Sillybutts/SLAB/SLAB v4 Release/STLs/Green/TopCover.stl

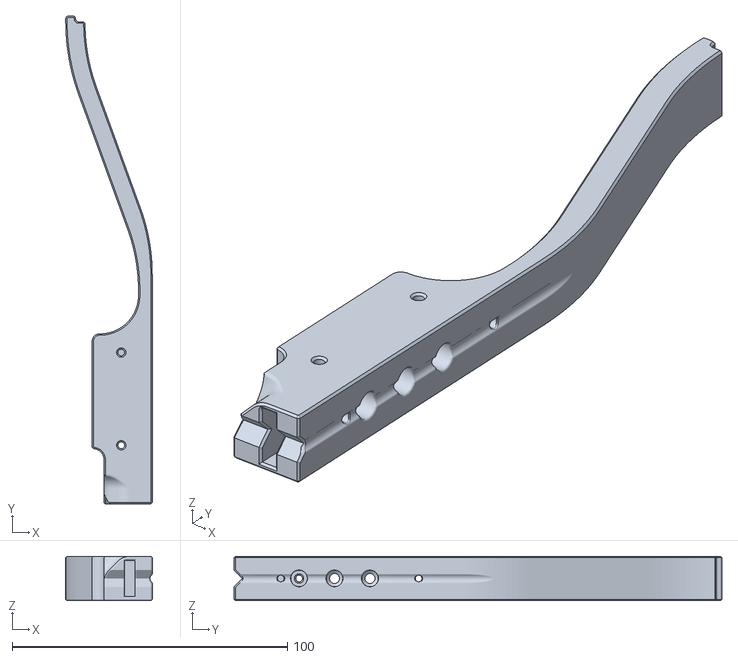
[picture p50: CAD file, 2023-04-10]
SLAB v4 Release/STLs/Green/TopCover.stl
31.4 x 177.2 x 16.1
