Sillybutts/SLAB/SLAB v4 Release/STLs/Orange/Trigger_ExperimentalMoreClearanceWithLever.stl

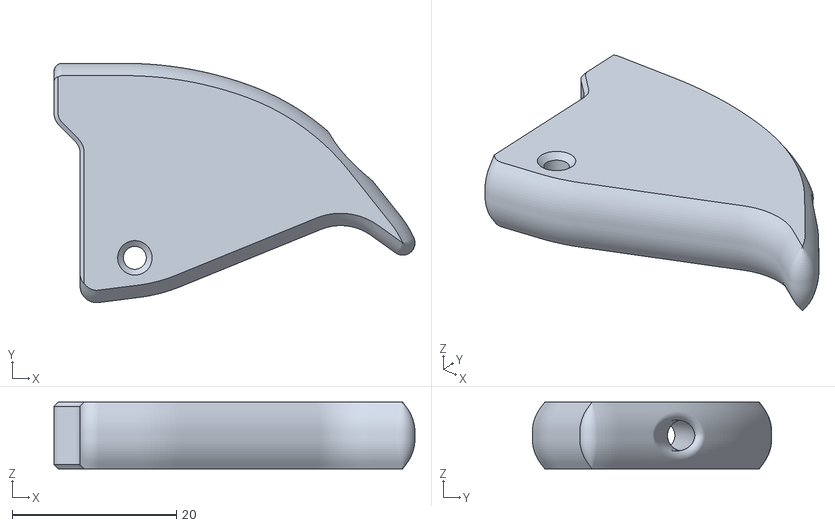
[picture p51: CAD file, 2023-03-18]
SLAB v4 Release/STLs/Orange/Trigger_ExperimentalMoreClearanceWithLever.stl
44.0 x 29.2 x 8.12
