Sillybutts/SLAB/SLAB v4 Release/STLs/White/RailSpacer.stl

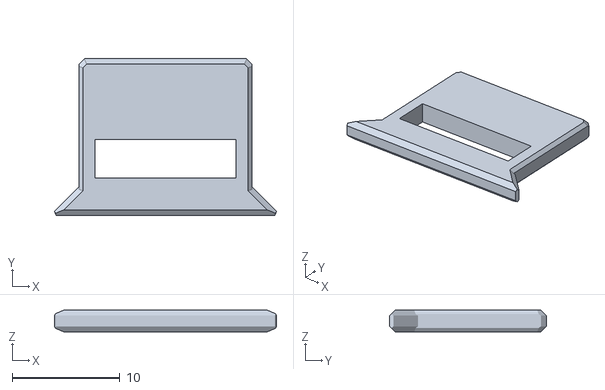
[picture p52: CAD file, 2023-03-18]
SLAB v4 Release/STLs/White/RailSpacer.stl
20.6 x 14.5 x 2.00
