Sillybutts/SLAB/v3 BAR BETA VERSION/v3 BAR BETA VERSION STLs/Black/StockButt.stl

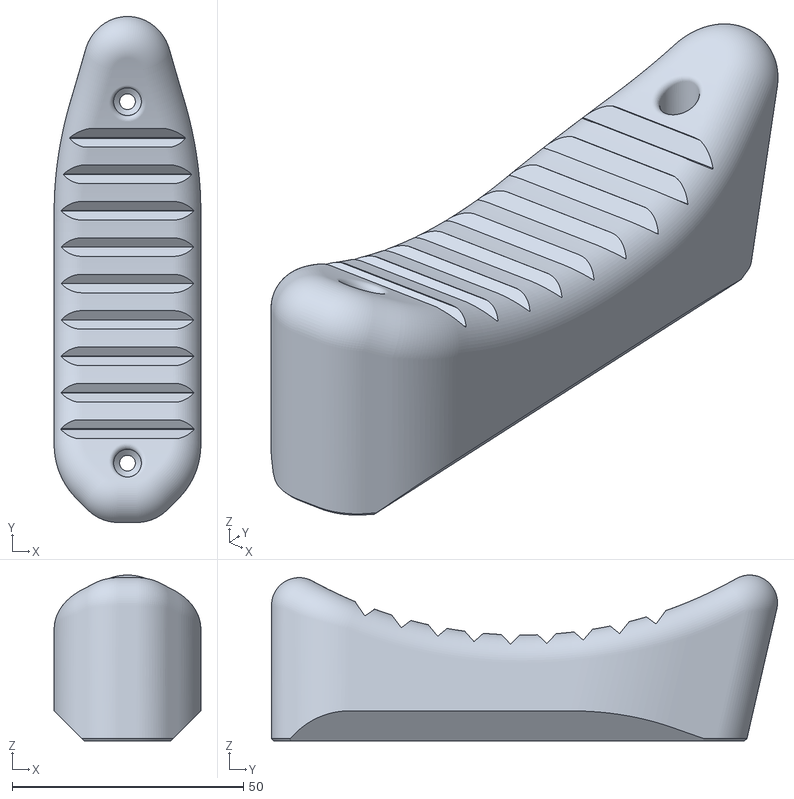
[picture p53: CAD file, 2022-07-23]
v3 BAR BETA VERSION/v3 BAR BETA VERSION STLs/Black/StockButt.stl
31.8 x 109.5 x 35.9
