Sillybutts/SLAB/v3 BAR BETA VERSION/v3 BAR BETA VERSION STLs/Green/New Backstrap.stl

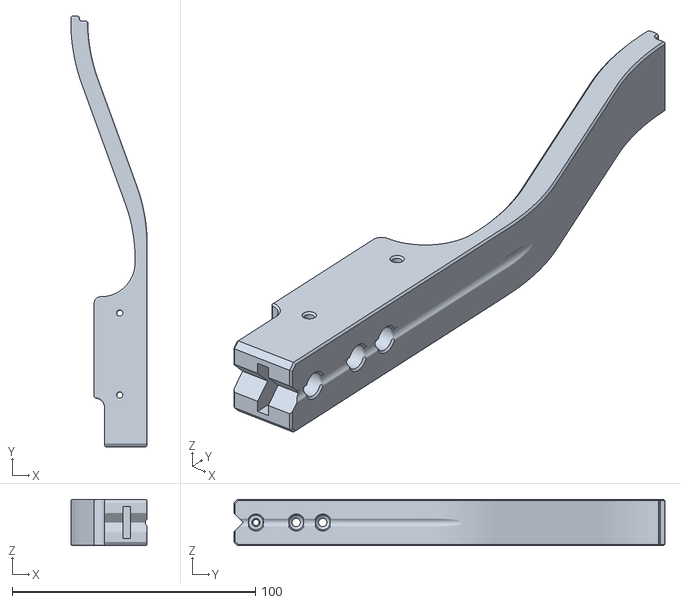
[picture p54: CAD file, 2022-08-06]
v3 BAR BETA VERSION/v3 BAR BETA VERSION STLs/Green/New Backstrap.stl
31.4 x 177.2 x 19.1
