Sillybutts/SLAB/v3 BAR BETA VERSION/v3 BAR BETA VERSION STLs/Orange/Bottlenose wRail.stl

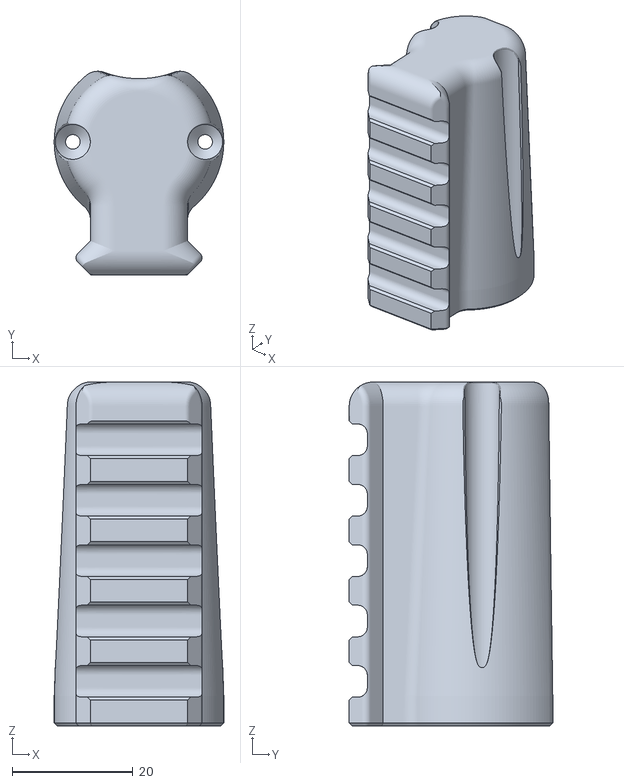
[picture p55: CAD file, 2022-08-02]
v3 BAR BETA VERSION/v3 BAR BETA VERSION STLs/Orange/Bottlenose wRail.stl
28.1 x 33.7 x 57.0
