Sillybutts/SLAB/v3 BAR BETA VERSION/v3 BAR BETA VERSION STLs/White/New Backrail.stl

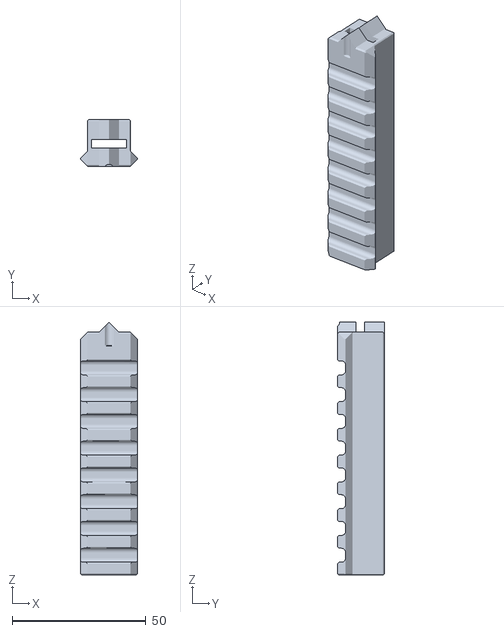
[picture p56: CAD file, 2022-08-06]
v3 BAR BETA VERSION/v3 BAR BETA VERSION STLs/White/New Backrail.stl
21.2 x 17.5 x 94.6
