Sillybutts/SLAB/SLAB Metric prints for the V4 3-10-2023/STLs/METRIC_Ram 7mmID o-ring.stl

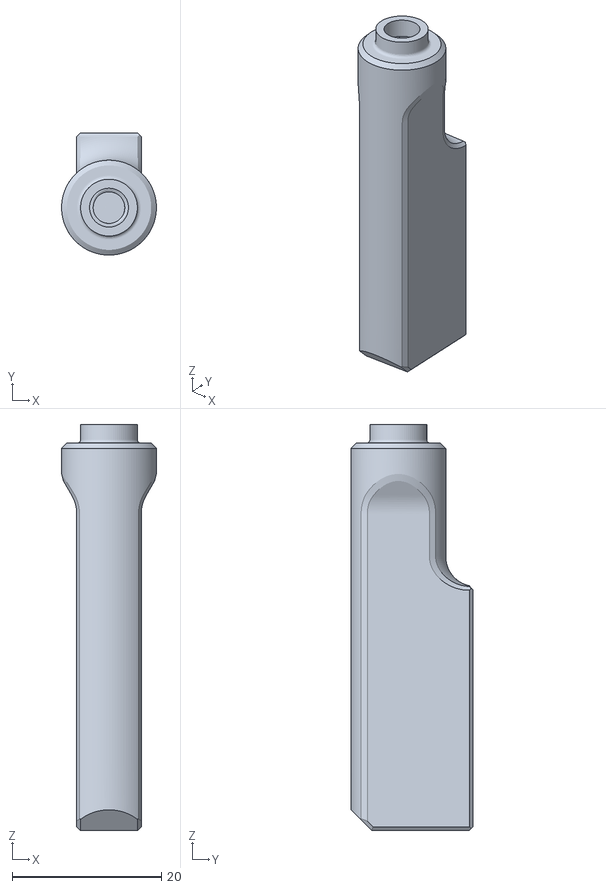
[picture p57: CAD file, 2023-03-10]
SLAB Metric prints for the V4 3-10-2023/STLs/METRIC_Ram 7mmID o-ring.stl
12.7 x 16.4 x 54.3
