Sillybutts/SLAB/SLAB v4 Release/STLs/Black/GripPanel_L.stl

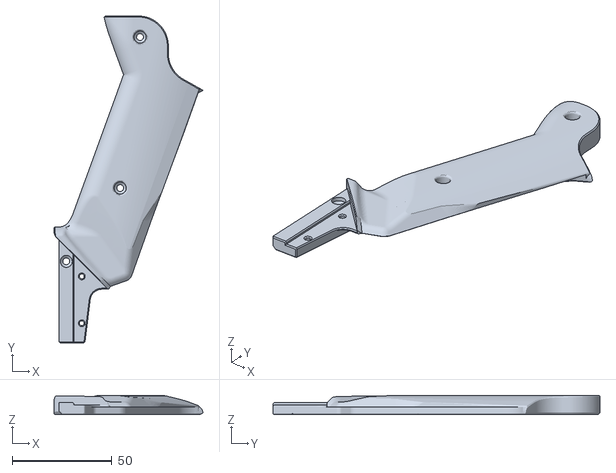
[picture p58: CAD file, 2023-03-18]
SLAB v4 Release/STLs/Black/GripPanel_L.stl
74.7 x 163.8 x 9.53
