Sillybutts/SLAB/SLAB v4 Release/STLs/EXPERIMENTAL AND OPTIONAL/Alternate logos/SideCover_L OLDLOGO.stl

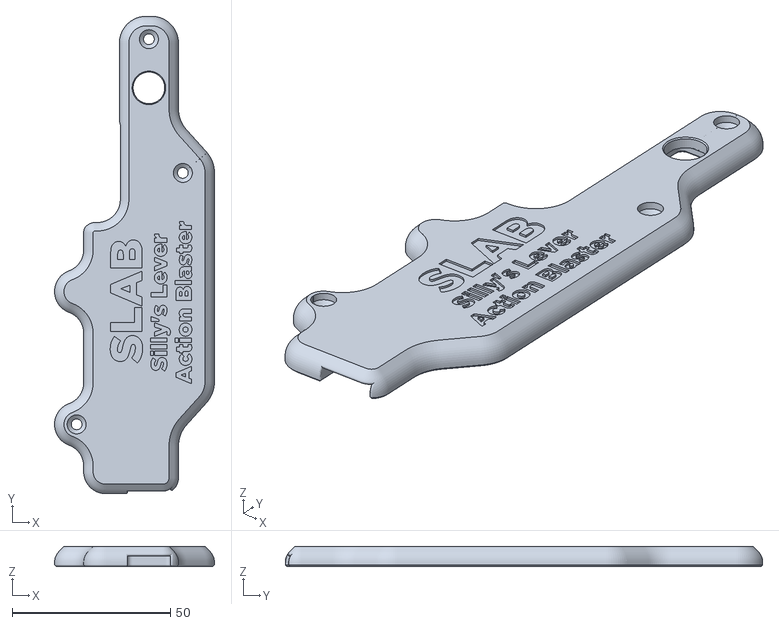
[picture p59: CAD file, 2023-03-18]
SLAB v4 Release/STLs/EXPERIMENTAL AND OPTIONAL/Alternate logos/SideCover_L OLDLOGO.stl
50.6 x 151.0 x 6.36
