Sillybutts/SLAB/SLAB v4 Release/STLs/EXPERIMENTAL AND OPTIONAL/Angled Talon magwell/Angled Magwell.stl

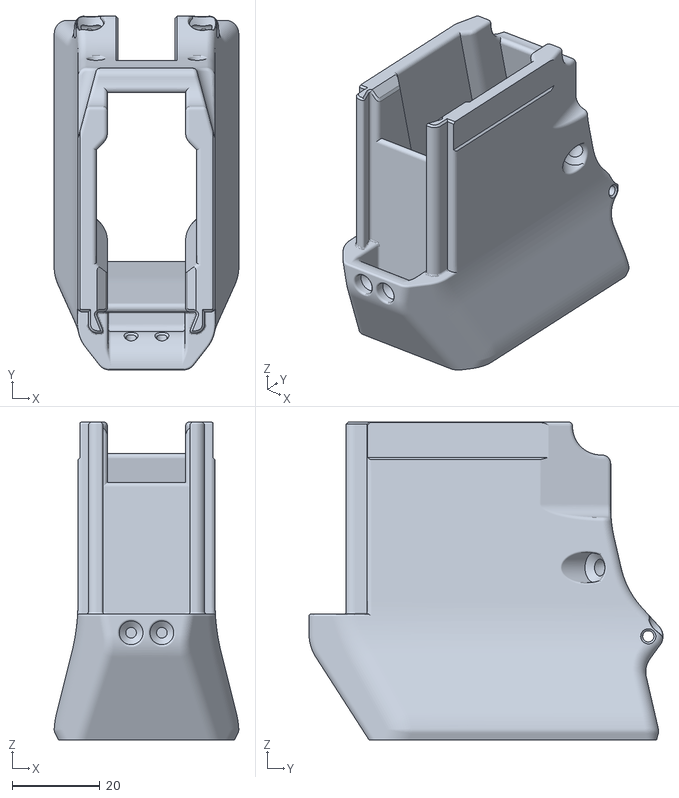
[picture p60: CAD file, 2023-03-18]
SLAB v4 Release/STLs/EXPERIMENTAL AND OPTIONAL/Angled Talon magwell/Angled Magwell.stl
42.0 x 80.6 x 72.4
