Sillybutts/SLAB/SLAB v4 Release/STLs/EXPERIMENTAL AND OPTIONAL/Long plunger rods that stick out the front/Muzzle_BottlenoseRail.stl

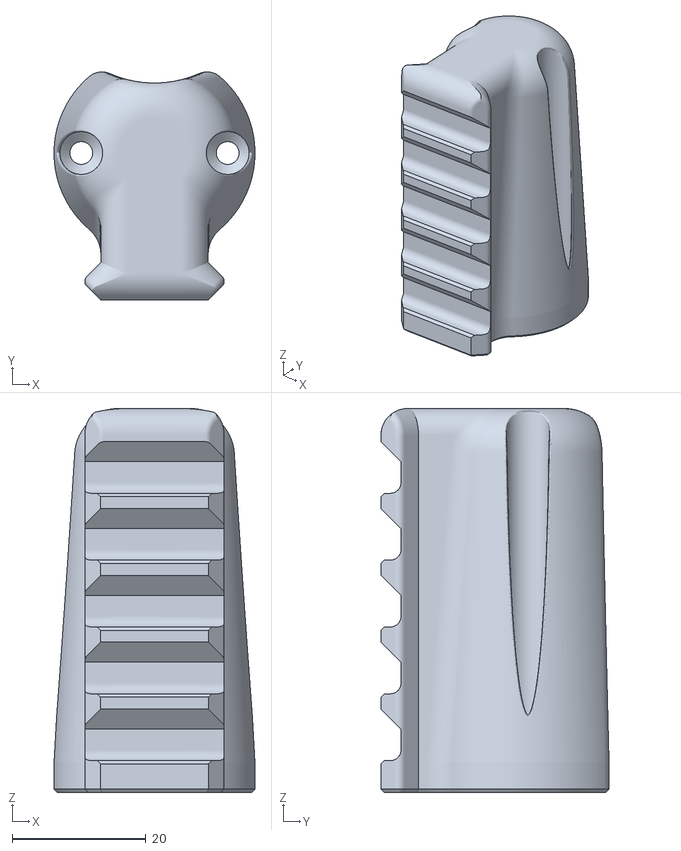
[picture p61: CAD file, 2023-03-18]
SLAB v4 Release/STLs/EXPERIMENTAL AND OPTIONAL/Long plunger rods that stick out the front/Muzzle_BottlenoseRail.stl
30.1 x 34.2 x 57.5
