Sillybutts/SLAB/SLAB v4 Release/STLs/EXPERIMENTAL AND OPTIONAL/Split lever for 150x150mm printers/Split_Lever_Standard.stl

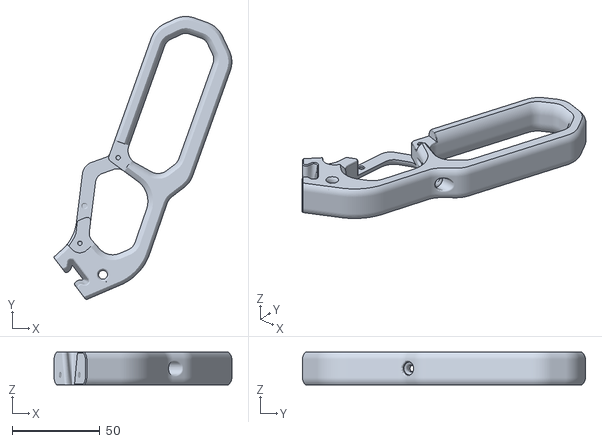
[picture p62: CAD file, 2023-03-18]
SLAB v4 Release/STLs/EXPERIMENTAL AND OPTIONAL/Split lever for 150x150mm printers/Split_Lever_Standard.stl
101.3 x 161.3 x 18.5
