Sillybutts/SLAB/SLAB v4 Release/STLs/Green/Handguard wShortPicatinny.stl

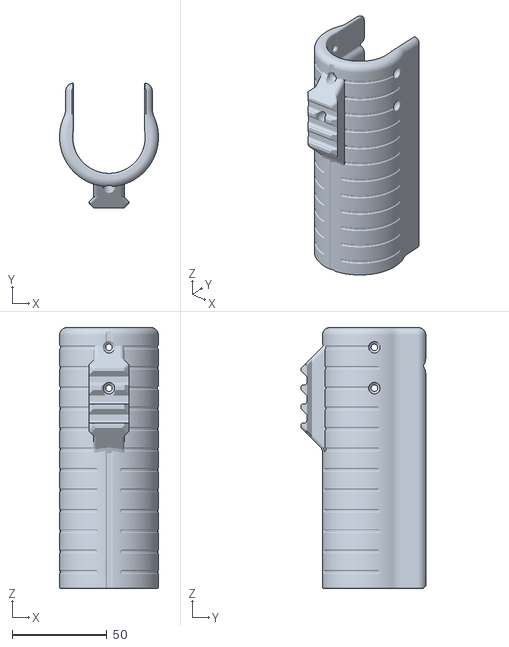
[picture p63: CAD file, 2023-04-10]
SLAB v4 Release/STLs/Green/Handguard wShortPicatinny.stl
52.1 x 65.6 x 137.4
