Sillybutts/SLAB/SLAB v4 Release/STLs/Orange/RodCapKeeper.stl

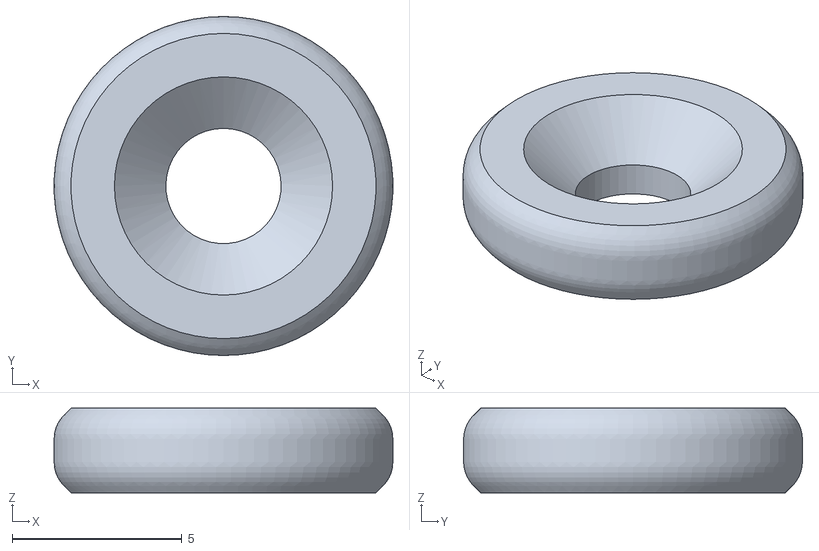
[picture p64: CAD file, 2023-03-18]
SLAB v4 Release/STLs/Orange/RodCapKeeper.stl
9.99 x 10.00 x 2.50
