Sillybutts/SLAB/SLAB v4 Release/STLs/White/RailB.stl

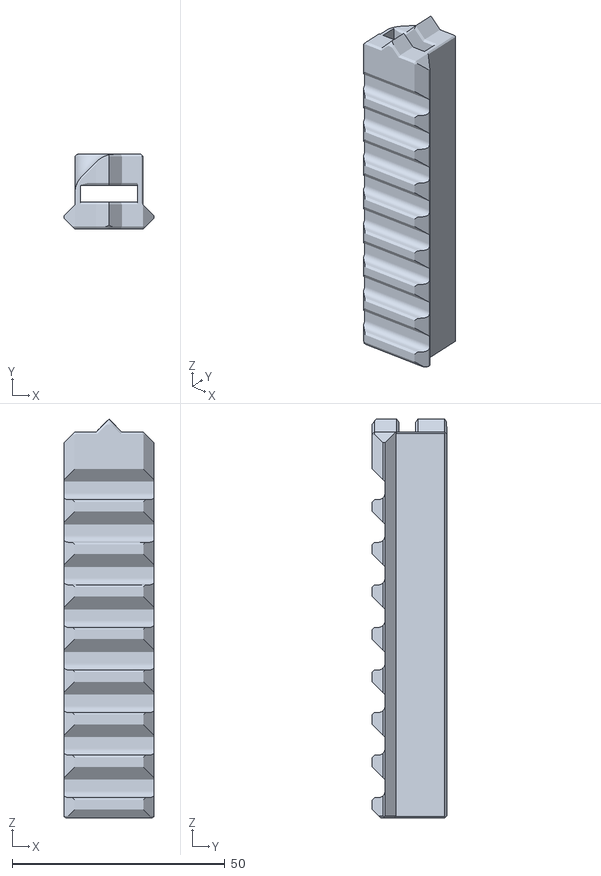
[picture p65: CAD file, 2023-03-18]
SLAB v4 Release/STLs/White/RailB.stl
21.2 x 17.5 x 93.8
