Sillybutts/SLAB/v3 BAR BETA VERSION/v3 BAR BETA VERSION STLs/Green/Handguard wBackstop.stl

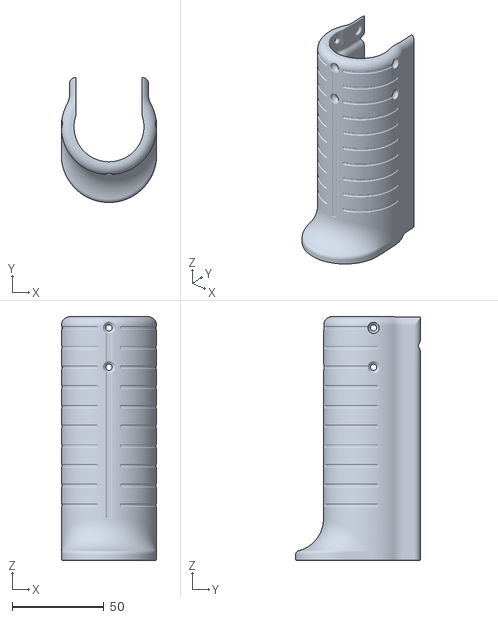
[picture p66: CAD file, 2022-08-06]
v3 BAR BETA VERSION/v3 BAR BETA VERSION STLs/Green/Handguard wBackstop.stl
52.1 x 68.3 x 133.2
