Sillybutts/SLAB/SLAB Metric prints for the V4 3-10-2023/STLs/METRIC_OnePieceTurnaround.stl

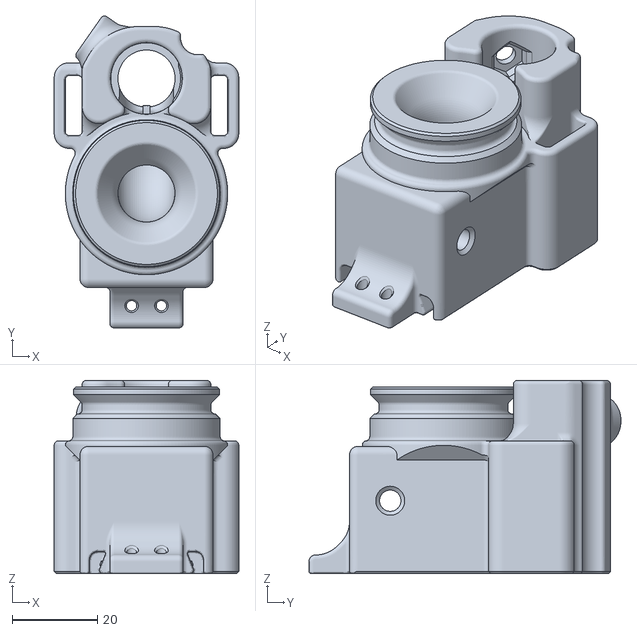
[picture p67: CAD file, 2023-03-10]
SLAB Metric prints for the V4 3-10-2023/STLs/METRIC_OnePieceTurnaround.stl
43.3 x 73.2 x 45.4
