Sillybutts/SLAB/SLAB v4 Release/STLs/EXPERIMENTAL AND OPTIONAL/Alternate logos/Nameplate.stl

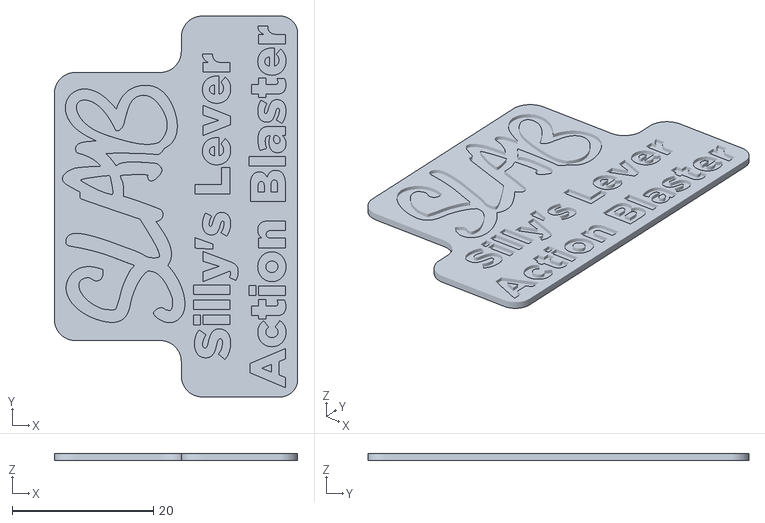
[picture p68: CAD file, 2023-03-18]
SLAB v4 Release/STLs/EXPERIMENTAL AND OPTIONAL/Alternate logos/Nameplate.stl
34.5 x 54.0 x 1.00
