Sillybutts/SLAB/SLAB v4 Release/STLs/EXPERIMENTAL AND OPTIONAL/Long plunger rods that stick out the front/Long PlungerRod ARMED.stl

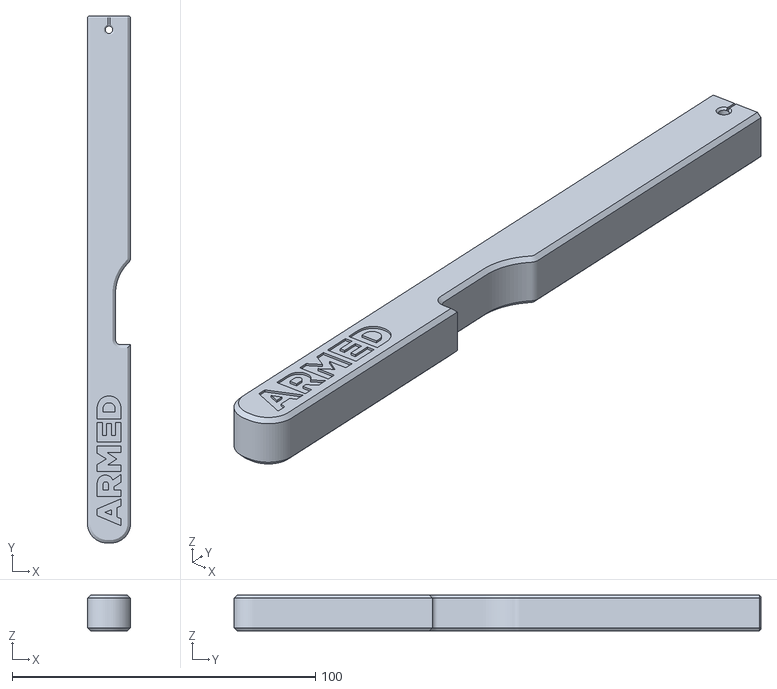
[picture p69: CAD file, 2023-03-18]
SLAB v4 Release/STLs/EXPERIMENTAL AND OPTIONAL/Long plunger rods that stick out the front/Long PlungerRod ARMED.stl
14.3 x 173.8 x 11.8
