Sillybutts/SLAB/SLAB v4 Release/STLs/EXPERIMENTAL AND OPTIONAL/No stock/StockCoreA Stockless.stl

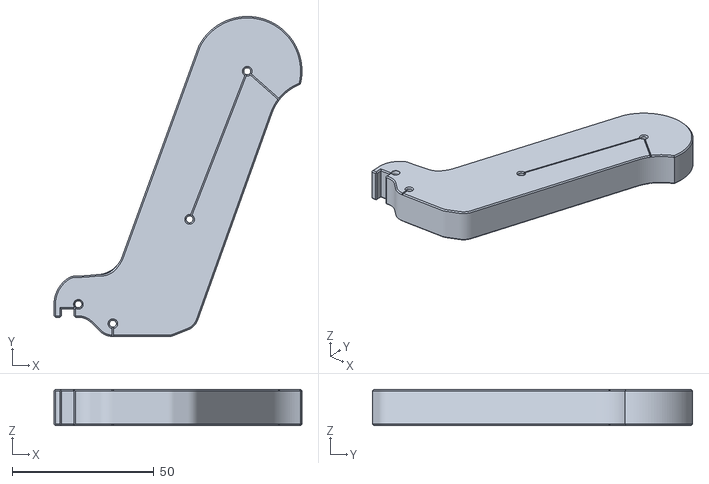
[picture p70: CAD file, 2023-03-18]
SLAB v4 Release/STLs/EXPERIMENTAL AND OPTIONAL/No stock/StockCoreA Stockless.stl
87.3 x 112.7 x 12.7
