Sillybutts/SLAB/SLAB v4 Release/STLs/EXPERIMENTAL AND OPTIONAL/Split lever for 150x150mm printers/Split_Lever_LeverTop.stl

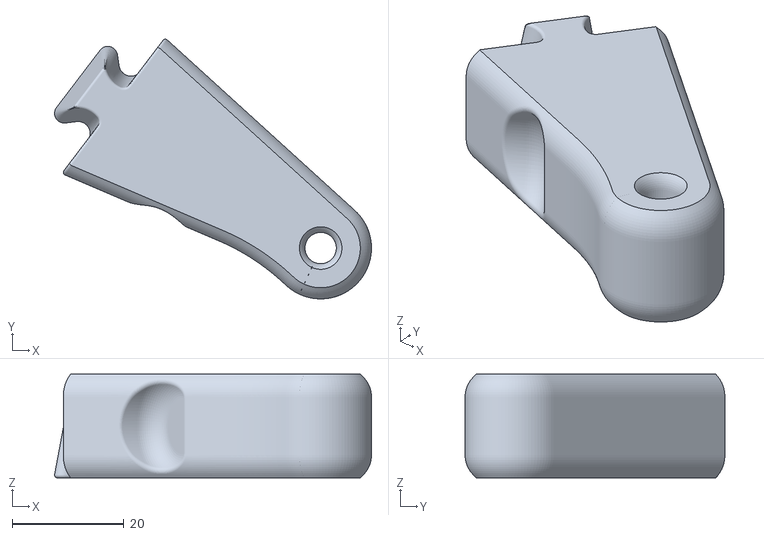
[picture p71: CAD file, 2023-03-18]
SLAB v4 Release/STLs/EXPERIMENTAL AND OPTIONAL/Split lever for 150x150mm printers/Split_Lever_LeverTop.stl
56.6 x 46.4 x 18.5
