Sillybutts/SLAB/SLAB v4 Release/STLs/Green/MuzzleB.stl

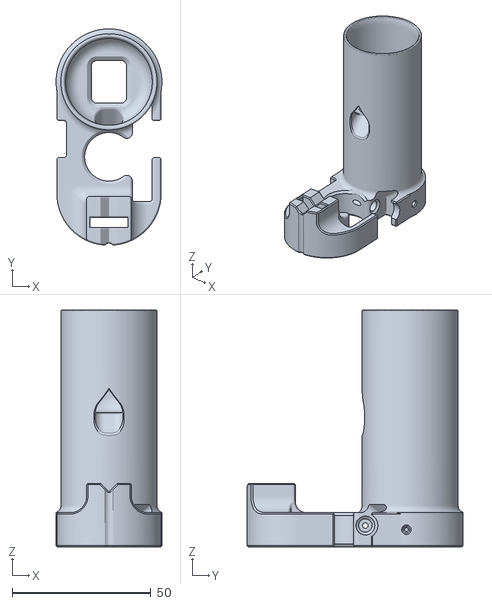
[picture p72: CAD file, 2023-03-18]
SLAB v4 Release/STLs/Green/MuzzleB.stl
38.1 x 77.8 x 85.3
