Sillybutts/SLAB/SLAB v4 Release/STLs/Orange/RodCapPivot.stl

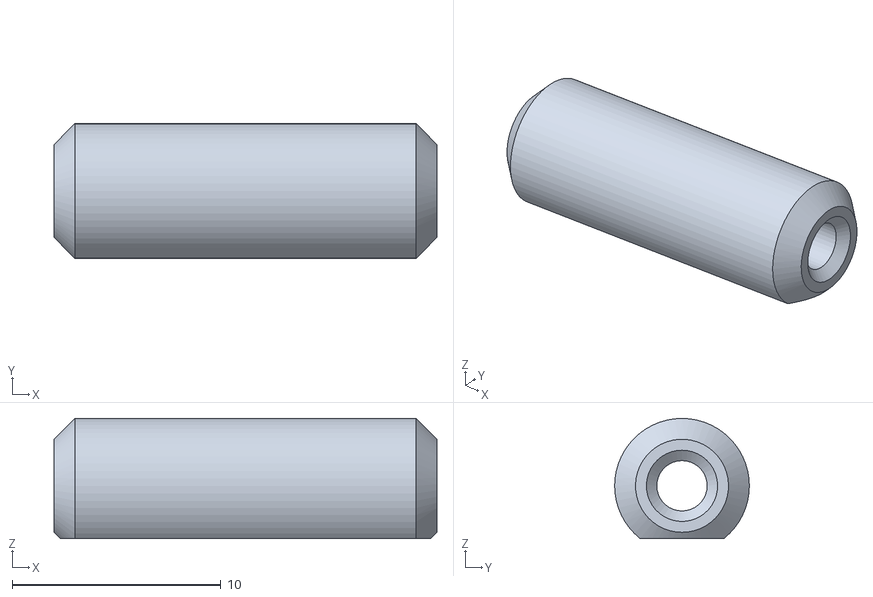
[picture p73: CAD file, 2023-03-18]
SLAB v4 Release/STLs/Orange/RodCapPivot.stl
18.4 x 6.46 x 5.76
