Sillybutts/SLAB/SLAB v4 Release/STLs/White/SightFront.stl

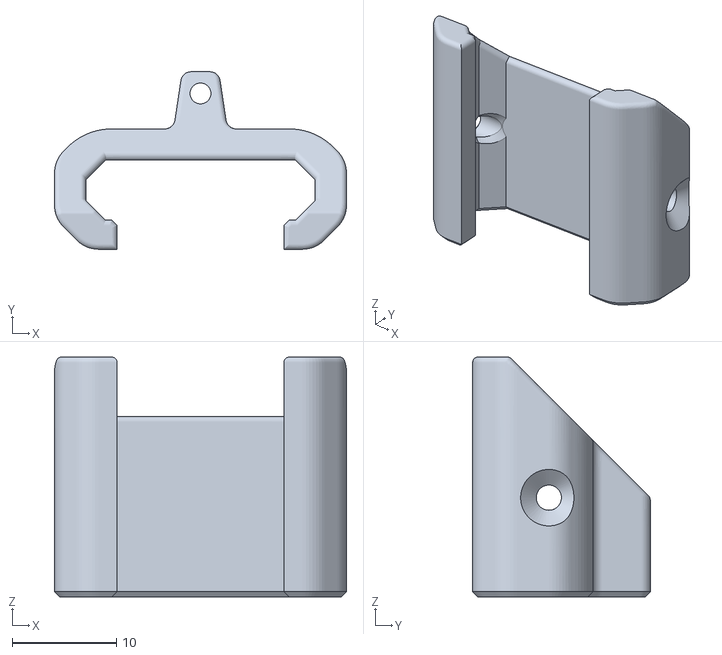
[picture p74: CAD file, 2023-03-18]
SLAB v4 Release/STLs/White/SightFront.stl
28.0 x 17.0 x 23.0
