Sillybutts/SLAB/v3 BAR BETA VERSION/v3 BAR BETA VERSION STLs/Black/Turnaround.stl

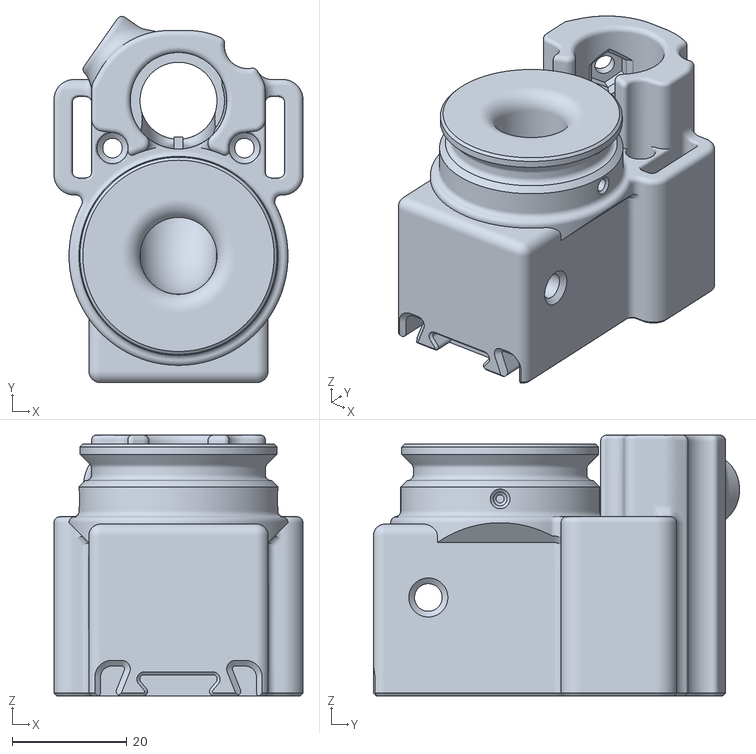
[picture p75: CAD file, 2022-07-20]
v3 BAR BETA VERSION/v3 BAR BETA VERSION STLs/Black/Turnaround.stl
43.3 x 63.7 x 45.4
