Sillybutts/SLAB/v3 BAR BETA VERSION/v3 BAR BETA VERSION STLs/Green/PrintedCotterPin.stl

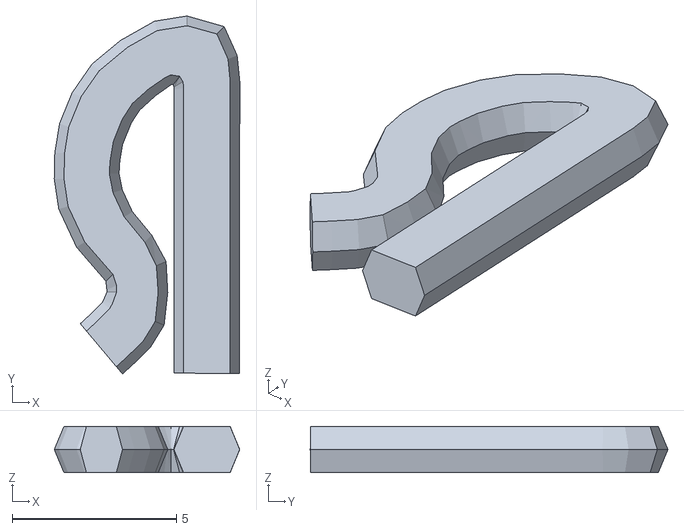
[picture p76: CAD file, 2022-07-25]
v3 BAR BETA VERSION/v3 BAR BETA VERSION STLs/Green/PrintedCotterPin.stl
5.65 x 10.9 x 1.41
