Sillybutts/SLAB/SLAB v4 Release/STLs/Black/PlungerRod.stl

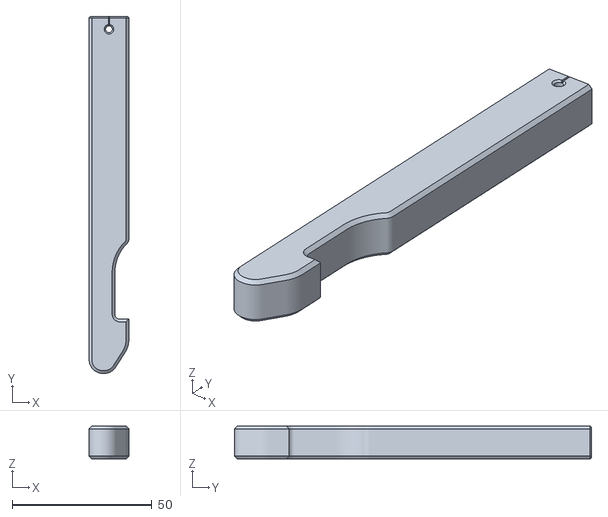
[picture p77: CAD file, 2023-03-18]
SLAB v4 Release/STLs/Black/PlungerRod.stl
14.3 x 127.9 x 11.8
