Sillybutts/SLAB/SLAB v4 Release/STLs/EXPERIMENTAL AND OPTIONAL/MegaXL Spigot SCAR/BarrelCap.stl

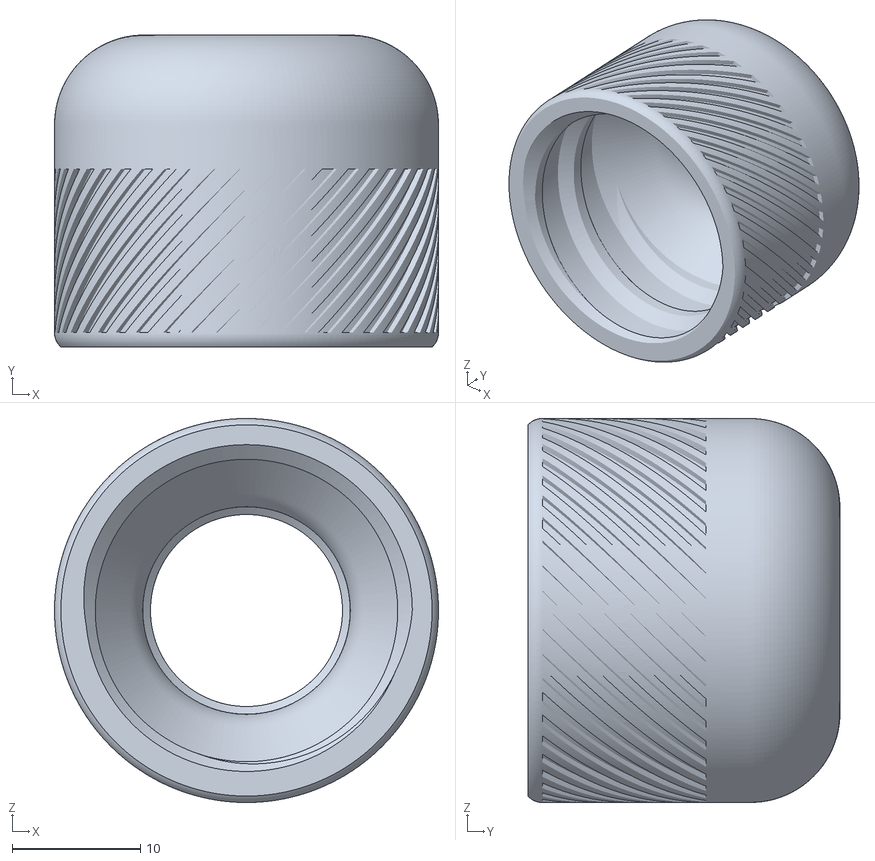
[picture p79: CAD file, 2022-08-25]
SLAB v4 Release/STLs/EXPERIMENTAL AND OPTIONAL/MegaXL Spigot SCAR/BarrelCap.stl
30.0 x 24.4 x 30.0
