Sillybutts/SLAB/SLAB v4 Release/STLs/EXPERIMENTAL AND OPTIONAL/Split lever for 150x150mm printers/Split_Lever_Big.stl

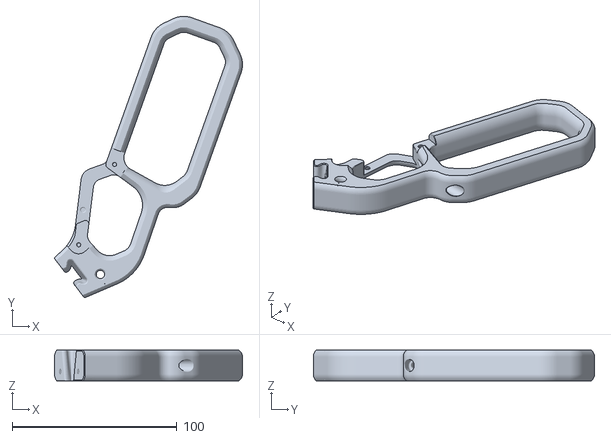
[picture p80: CAD file, 2023-03-18]
SLAB v4 Release/STLs/EXPERIMENTAL AND OPTIONAL/Split lever for 150x150mm printers/Split_Lever_Big.stl
114.1 x 170.8 x 18.5
