Sillybutts/SLAB/SLAB v4 Release/STLs/Green/StockPanelB_R.stl

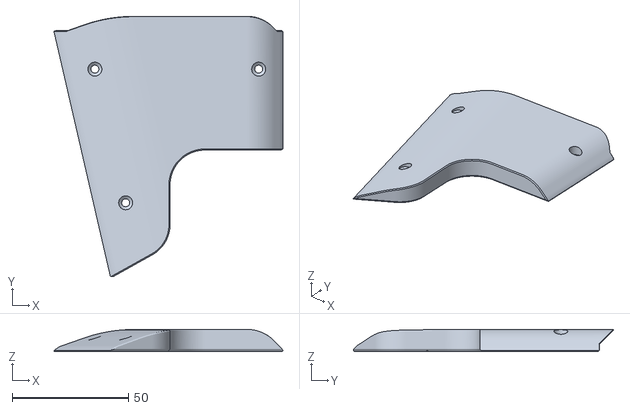
[picture p81: CAD file, 2023-03-18]
SLAB v4 Release/STLs/Green/StockPanelB_R.stl
98.5 x 112.0 x 9.53
