Sillybutts/SLAB/SLAB v4 Release/STLs/White/Railless_RailA.stl

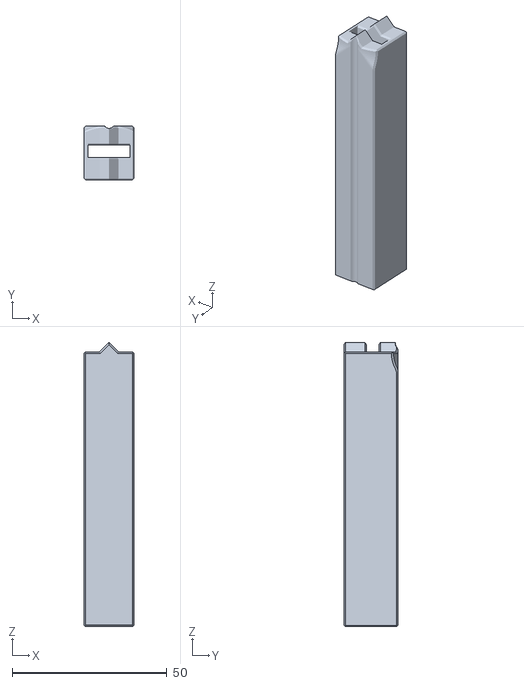
[picture p82: CAD file, 2023-03-18]
SLAB v4 Release/STLs/White/Railless_RailA.stl
16.1 x 17.5 x 91.8
