Sillybutts/SLAB/v3 BAR BETA VERSION/v3 BAR BETA VERSION STLs/Black/PlungerRod ARMED.stl

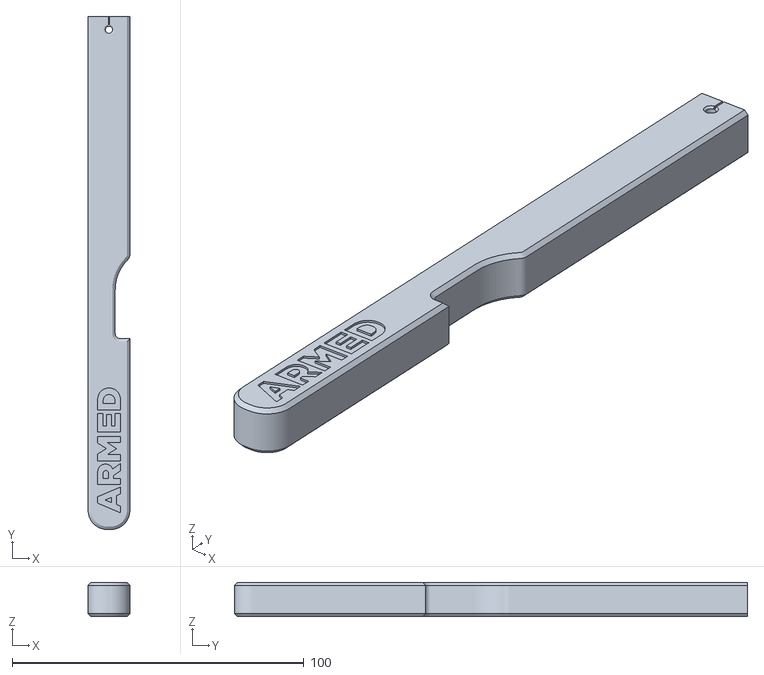
[picture p83: CAD file, 2022-06-17]
v3 BAR BETA VERSION/v3 BAR BETA VERSION STLs/Black/PlungerRod ARMED.stl
14.3 x 175.8 x 11.8
