Sillybutts/SLAB/SLAB Metric prints for the V4 3-10-2023/STLs/SplitTurnaroundCap.stl

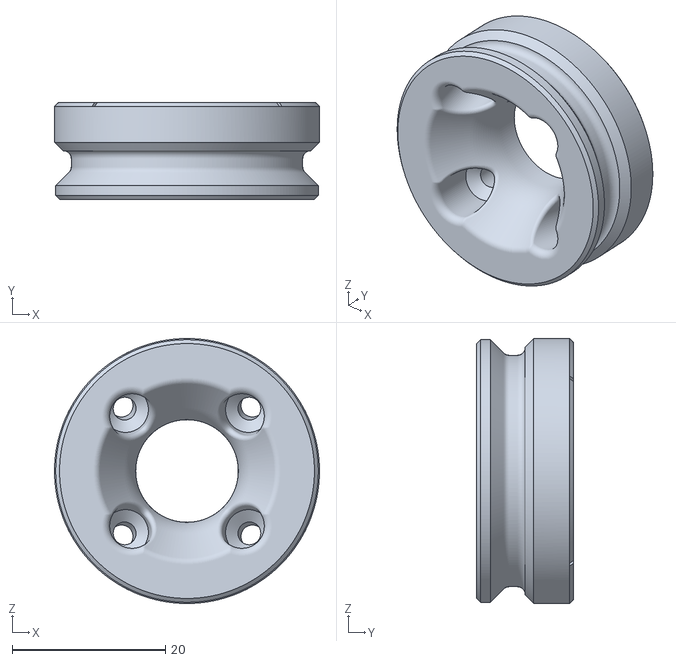
[picture p84: CAD file, 2023-02-27]
SLAB Metric prints for the V4 3-10-2023/STLs/SplitTurnaroundCap.stl
34.6 x 12.7 x 34.6
