Sillybutts/SLAB/SLAB v4 Release/STLs/EXPERIMENTAL AND OPTIONAL/Long plunger rods that stick out the front/Muzzle_Bottlenose.stl

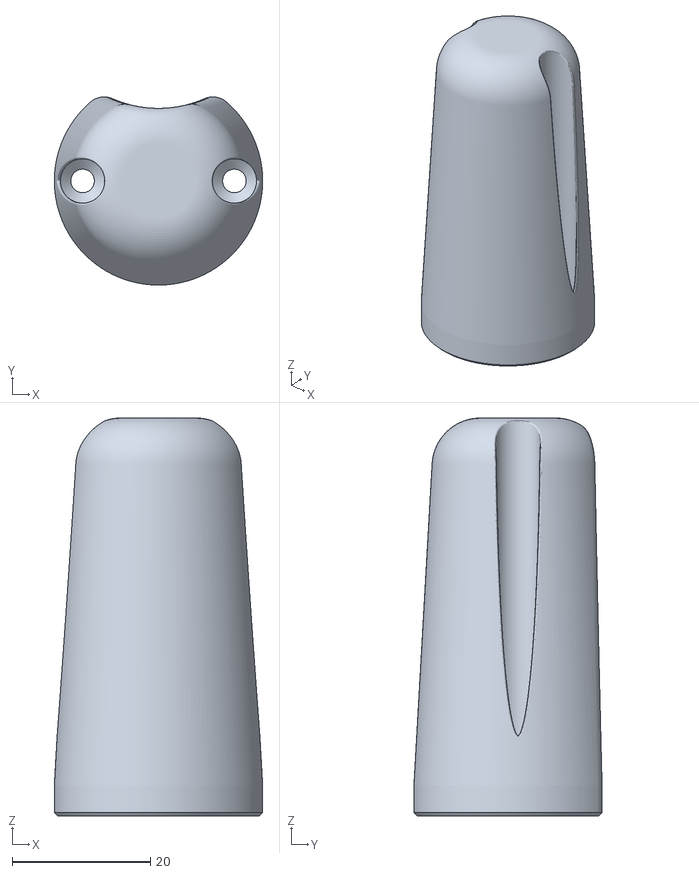
[picture p85: CAD file, 2023-03-18]
SLAB v4 Release/STLs/EXPERIMENTAL AND OPTIONAL/Long plunger rods that stick out the front/Muzzle_Bottlenose.stl
30.1 x 27.2 x 57.5
