Sillybutts/SLAB/SLAB v4 Release/STLs/Green/StockPanelA_R.stl

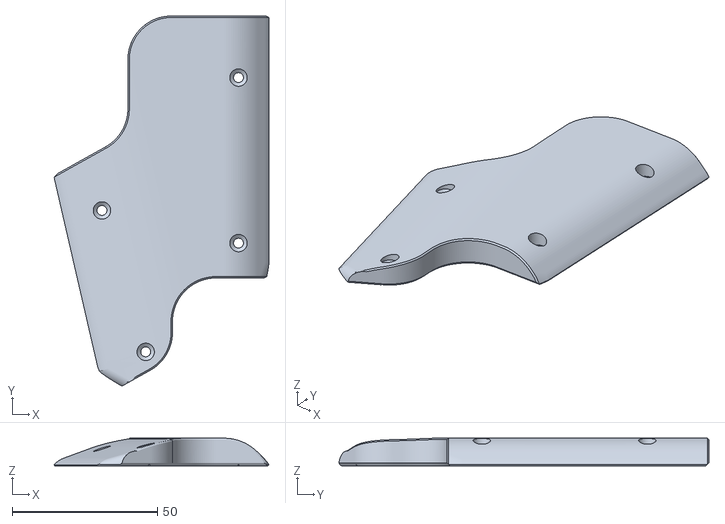
[picture p86: CAD file, 2023-03-18]
SLAB v4 Release/STLs/Green/StockPanelA_R.stl
74.0 x 127.4 x 9.53
