Sillybutts/SLAB/SLAB v4 Release/STLs/Orange/Ram_FlatFace_Tighter.stl

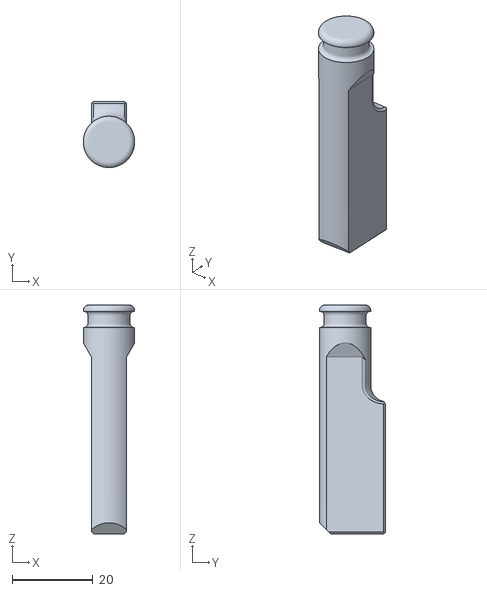
[picture p87: CAD file, 2023-03-18]
SLAB v4 Release/STLs/Orange/Ram_FlatFace_Tighter.stl
12.7 x 16.4 x 56.6
