Sillybutts/SLAB/SLAB v4 Release/STLs/White/Railless_RailB.stl

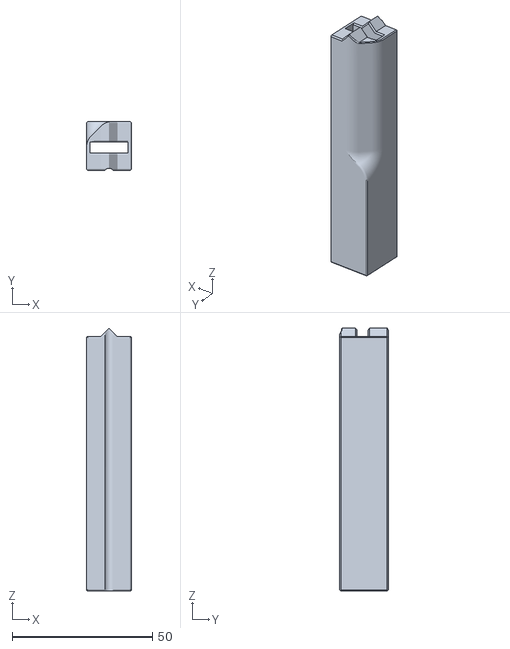
[picture p88: CAD file, 2023-03-18]
SLAB v4 Release/STLs/White/Railless_RailB.stl
16.1 x 17.5 x 93.8
