Sillybutts/SLAB/v3 BAR BETA VERSION/v3 BAR BETA VERSION STLs/Black/PlungerRod BLANK.stl

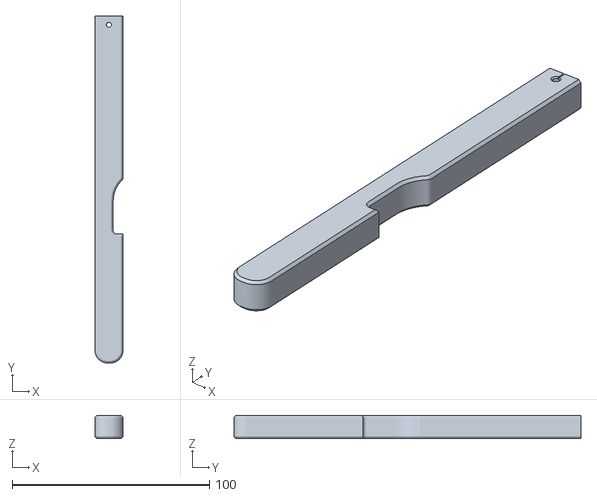
[picture p89: CAD file, 2022-06-17]
v3 BAR BETA VERSION/v3 BAR BETA VERSION STLs/Black/PlungerRod BLANK.stl
14.3 x 175.8 x 11.8
