Sillybutts/SLAB/SLAB v4 Release/STLs/Black/OptionalTopCoverTopRail.stl

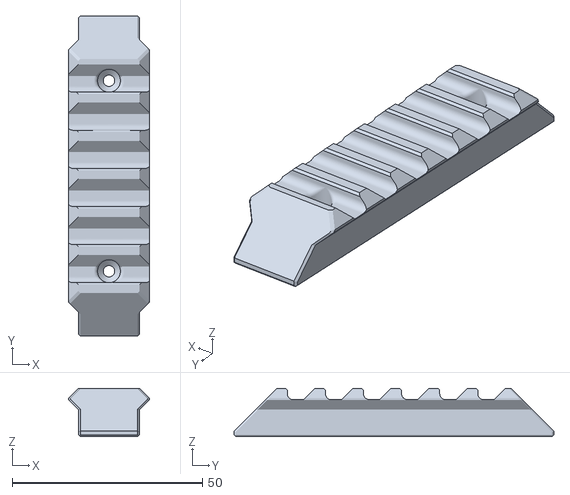
[picture p90: CAD file, 2023-03-18]
SLAB v4 Release/STLs/Black/OptionalTopCoverTopRail.stl
21.2 x 84.1 x 12.7
