Sillybutts/SLAB/SLAB v4 Release/STLs/EXPERIMENTAL AND OPTIONAL/Long plunger rods that stick out the front/Muzzle_FrontSlingOpen.stl

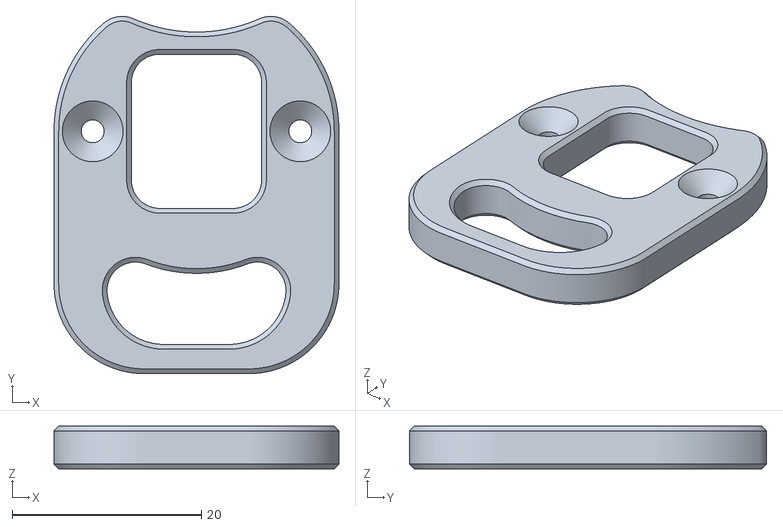
[picture p91: CAD file, 2023-03-18]
SLAB v4 Release/STLs/EXPERIMENTAL AND OPTIONAL/Long plunger rods that stick out the front/Muzzle_FrontSlingOpen.stl
30.1 x 37.7 x 4.50
