Sillybutts/SLAB/SLAB v4 Release/STLs/Green/SideCover_R wLogo.stl

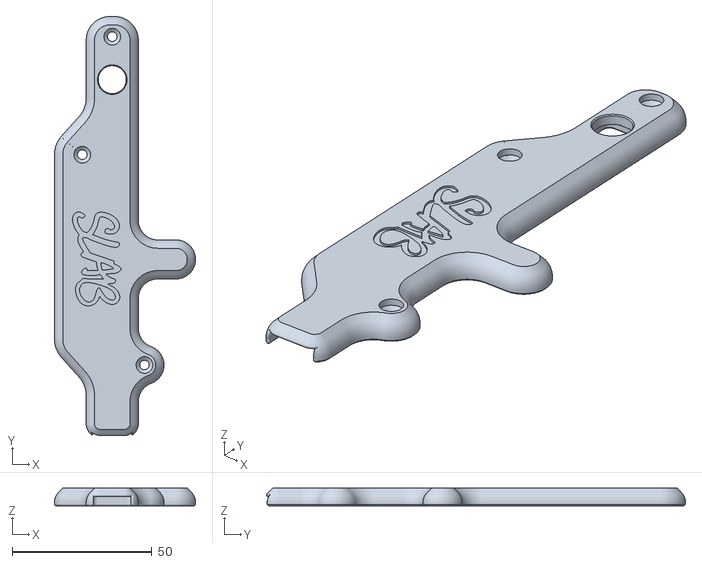
[picture p92: CAD file, 2023-03-18]
SLAB v4 Release/STLs/Green/SideCover_R wLogo.stl
50.6 x 150.2 x 6.36
