Sillybutts/SLAB/SLAB v4 Release/STLs/Orange/Catch.stl

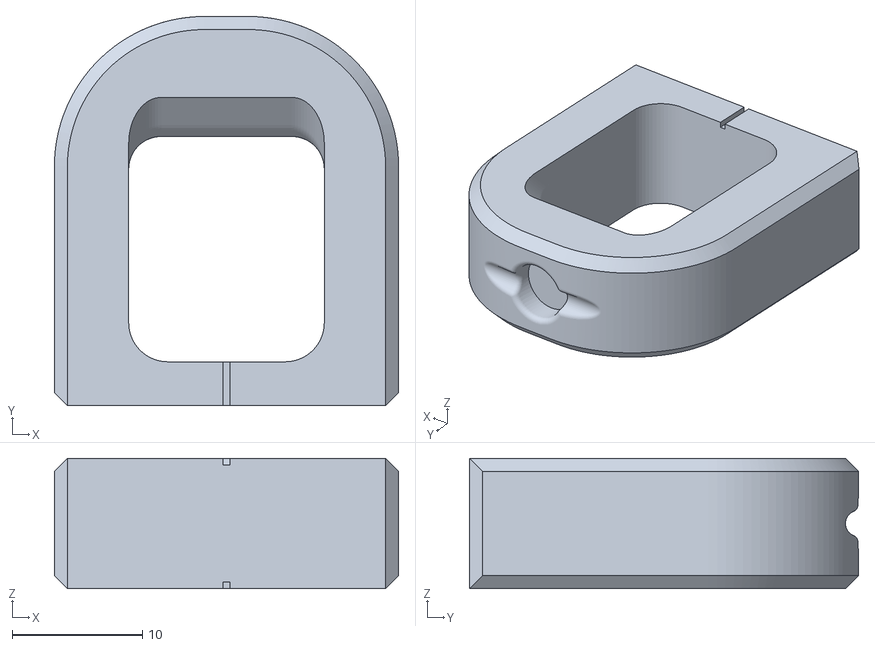
[picture p93: CAD file, 2023-03-18]
SLAB v4 Release/STLs/Orange/Catch.stl
26.4 x 29.8 x 10.0
