Sillybutts/SLAB/SLAB v4 Release/STLs/White/RailA.stl

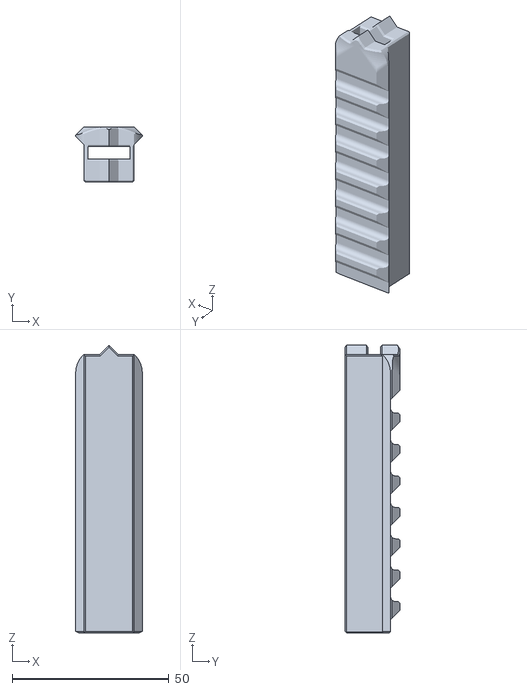
[picture p94: CAD file, 2023-03-18]
SLAB v4 Release/STLs/White/RailA.stl
21.2 x 17.5 x 91.8
