Sillybutts/SLAB/v3 BAR BETA VERSION/v3 BAR BETA VERSION STLs/Green/SideCover_R.stl

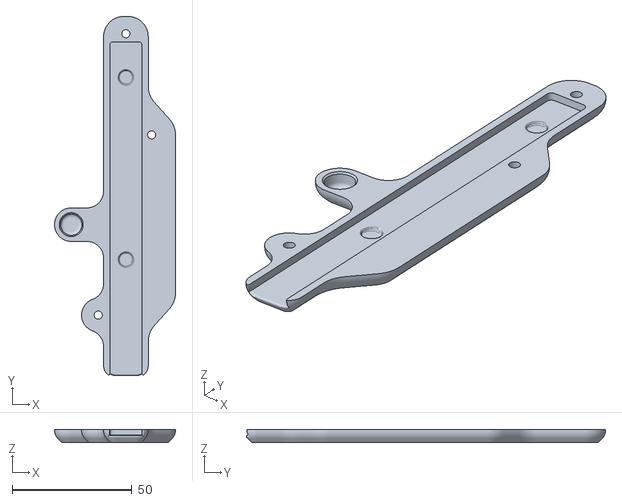
[picture p95: CAD file, 2022-07-03]
v3 BAR BETA VERSION/v3 BAR BETA VERSION STLs/Green/SideCover_R.stl
50.6 x 150.2 x 5.36
