Sillybutts/SLAB/SLAB v4 Release/STLs/Orange/PrimingBarSpacer (PRINT 2).stl

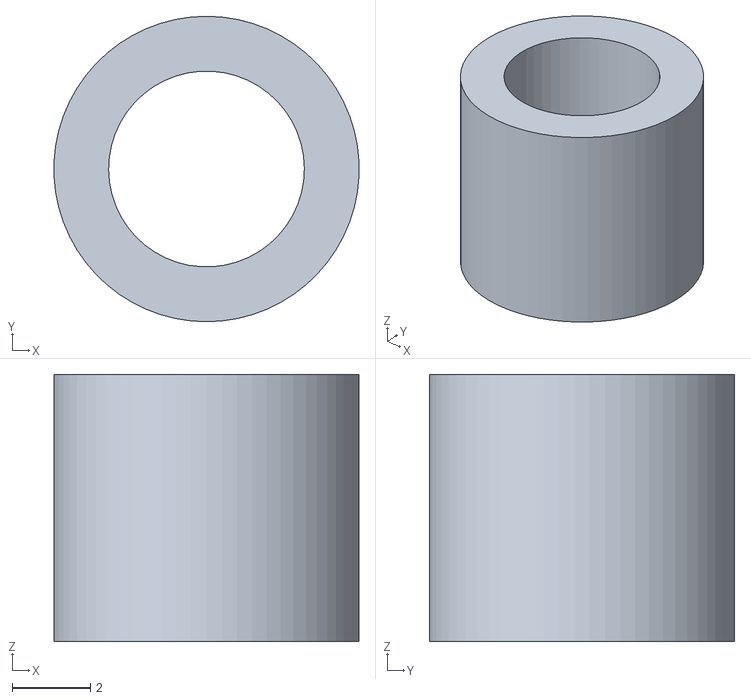
[picture p96: CAD file, 2023-03-18]
SLAB v4 Release/STLs/Orange/PrimingBarSpacer (PRINT 2).stl
7.79 x 7.80 x 6.83
