Sillybutts/SLAB/SLAB v4 Release/STLs/White/Magwell.stl

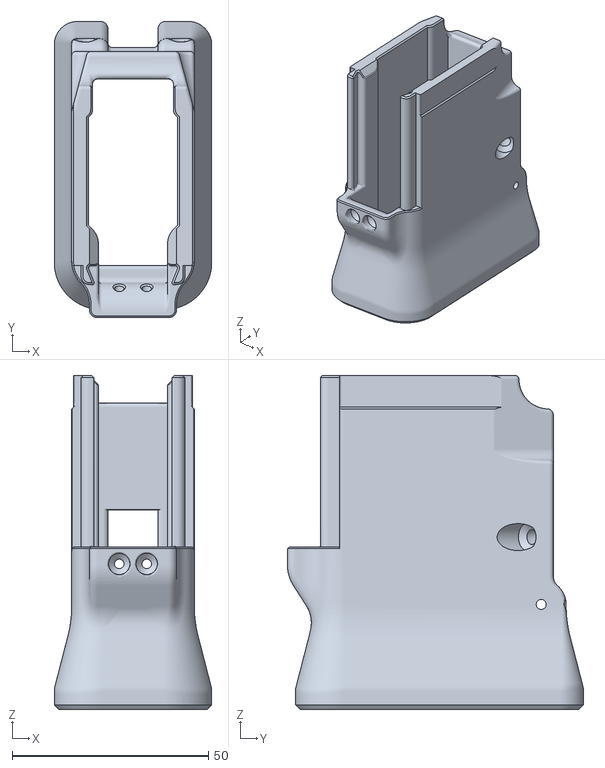
[picture p97: CAD file, 2023-03-18]
SLAB v4 Release/STLs/White/Magwell.stl
40.1 x 75.4 x 85.0
