Sillybutts/SLAB/v3 BAR BETA VERSION/v3 BAR BETA VERSION STLs/Green/SideCover_L.stl

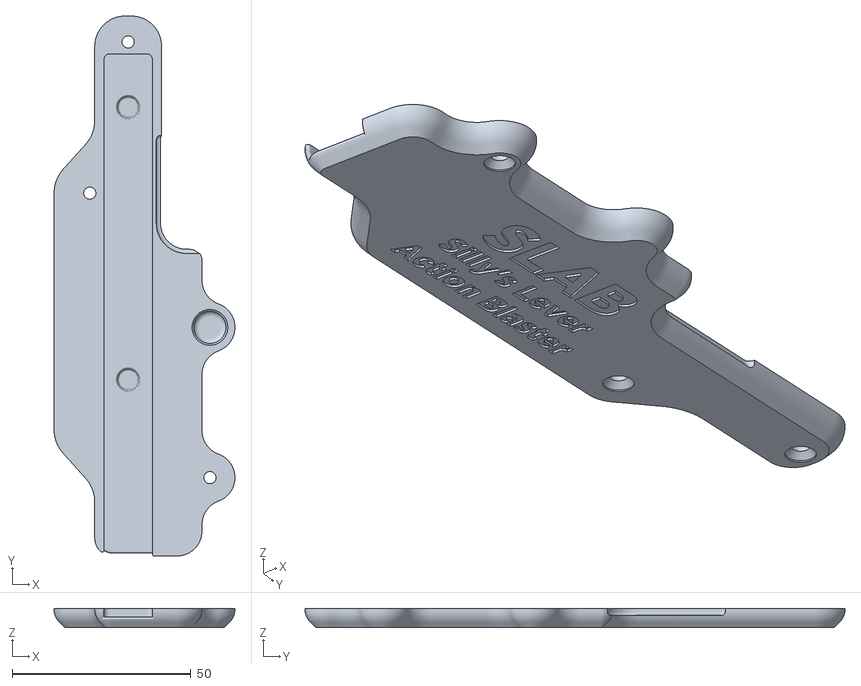
[picture p98: CAD file, 2022-07-03]
v3 BAR BETA VERSION/v3 BAR BETA VERSION STLs/Green/SideCover_L.stl
50.6 x 151.0 x 5.36
