Sillybutts/SLAB/v3 BAR BETA VERSION/v3 BAR BETA VERSION STLs/Orange/Ram.stl

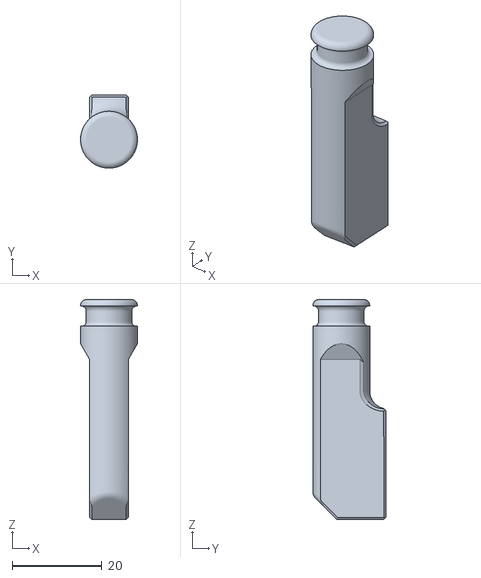
[picture p99: CAD file, 2022-07-20]
v3 BAR BETA VERSION/v3 BAR BETA VERSION STLs/Orange/Ram.stl
12.7 x 16.3 x 49.1
