Sillybutts/SLAB/SLAB v4 Release/STLs/Green/PrimeTransferBar.stl

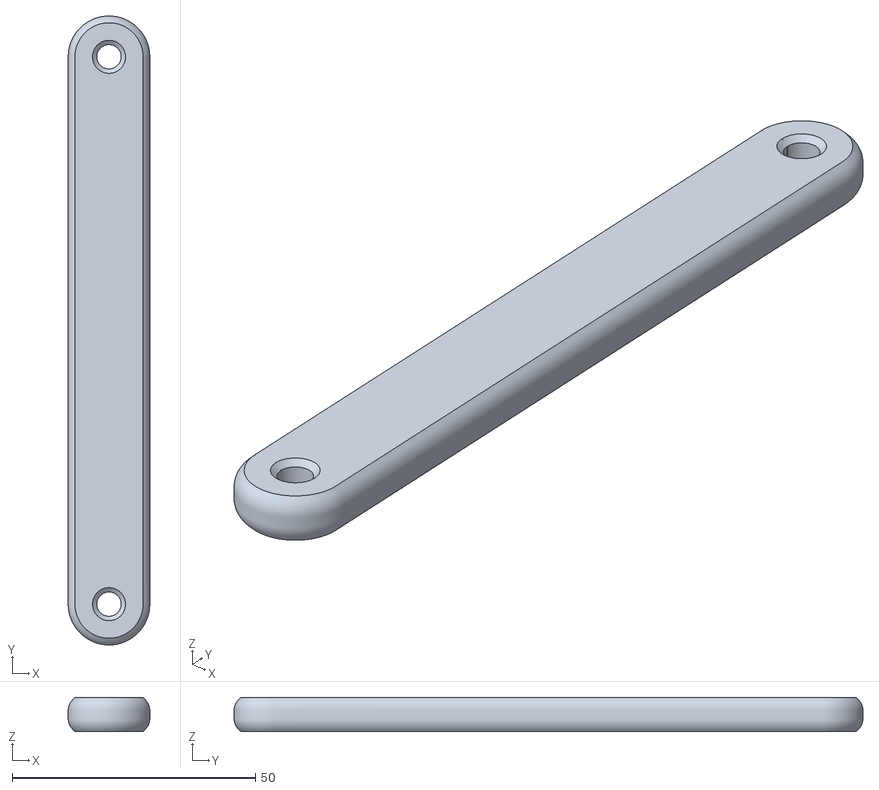
[picture p101: CAD file, 2023-03-18]
SLAB v4 Release/STLs/Green/PrimeTransferBar.stl
16.8 x 129.4 x 7.00
