Sillybutts/SLAB/SLAB v4 Release/STLs/Orange/TriggerBlock.stl

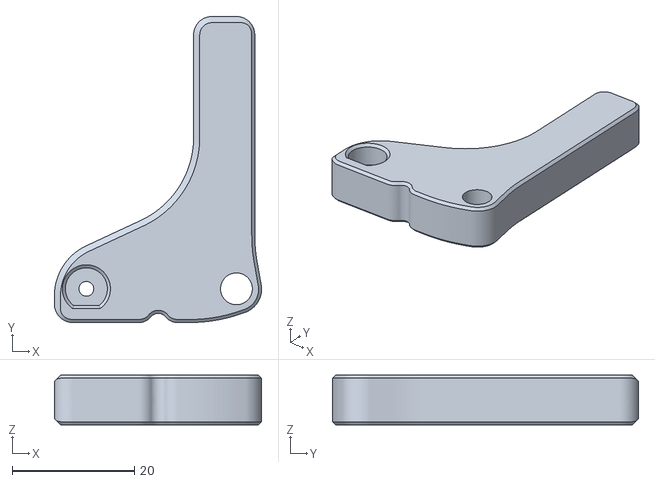
[picture p102: CAD file, 2023-03-18]
SLAB v4 Release/STLs/Orange/TriggerBlock.stl
33.9 x 50.0 x 8.12
