Sillybutts/SLAB/SLAB v4 Release/STLs/White/SightBack.stl

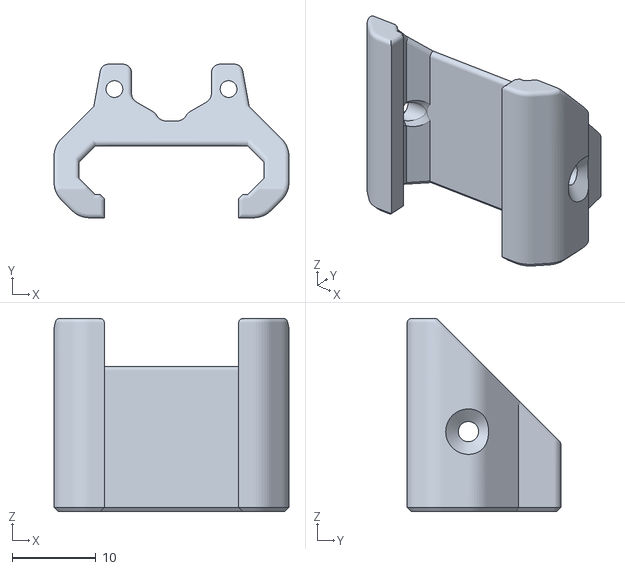
[picture p103: CAD file, 2023-03-18]
SLAB v4 Release/STLs/White/SightBack.stl
28.0 x 18.3 x 23.0
