Sillybutts/SLAB/SLAB v4 Release/STLs/Orange/Muzzle_EndCap.stl

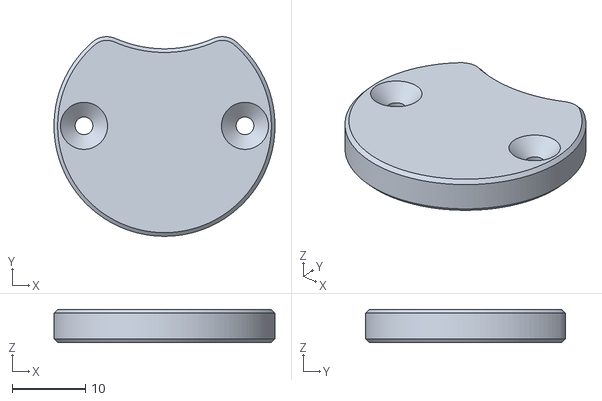
[picture p104: CAD file, 2023-03-18]
SLAB v4 Release/STLs/Orange/Muzzle_EndCap.stl
30.1 x 27.2 x 4.50
