Sillybutts/SLAB/SLAB v4 Release/STLs/White/FeedGuide.stl

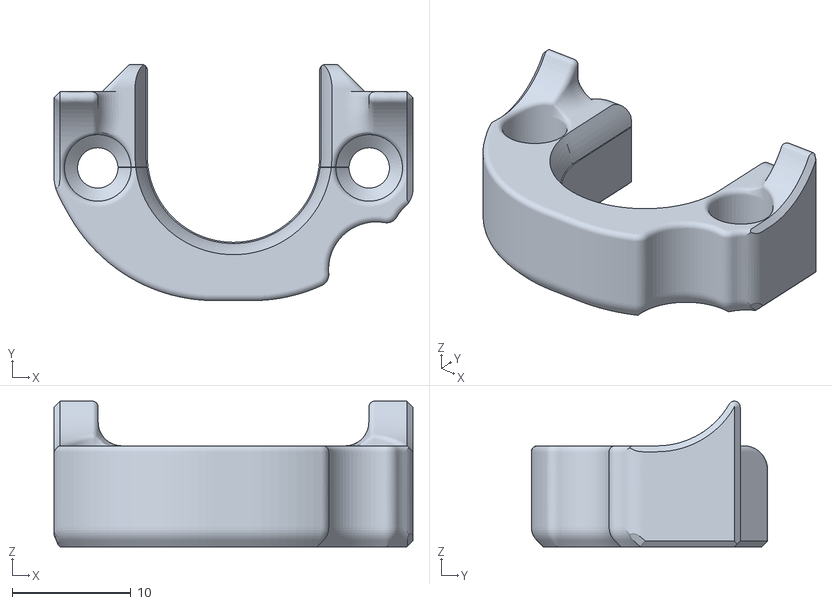
[picture p105: CAD file, 2023-03-18]
SLAB v4 Release/STLs/White/FeedGuide.stl
30.2 x 19.9 x 12.3
