Sillybutts/SLAB/v3 BAR BETA VERSION/v3 BAR BETA VERSION STLs/Orange/Front Sling.stl

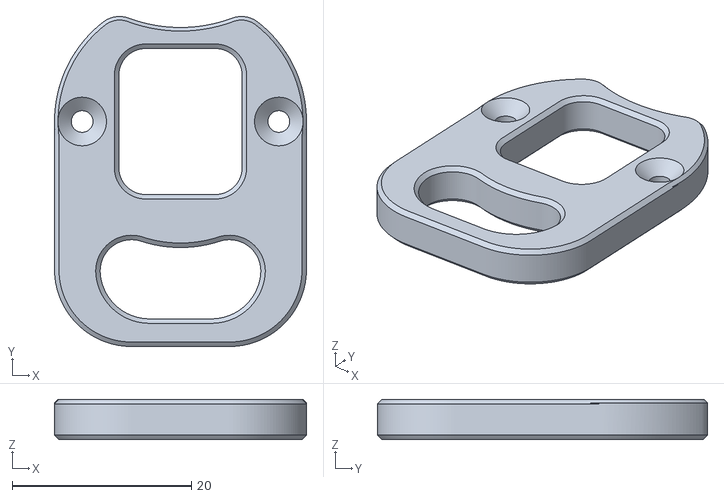
[picture p106: CAD file, 2022-07-20]
v3 BAR BETA VERSION/v3 BAR BETA VERSION STLs/Orange/Front Sling.stl
28.1 x 36.8 x 4.50
