Sillybutts/SLAB/SLAB v4 Release/STLs/Green/StockCoreB.stl

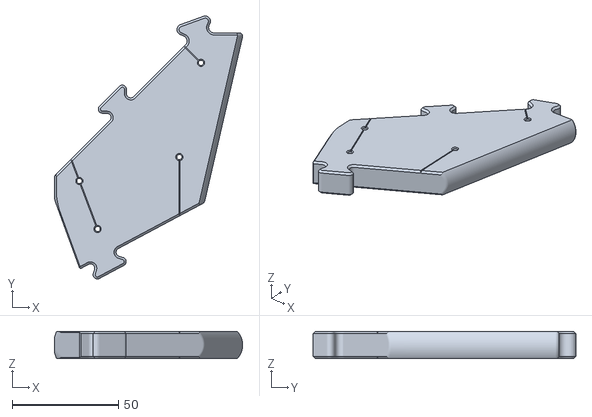
[picture p107: CAD file, 2023-03-18]
SLAB v4 Release/STLs/Green/StockCoreB.stl
88.6 x 123.7 x 12.7
