Sillybutts/SLAB/SLAB v4 Release/STLs/Orange/LeverBrace.stl

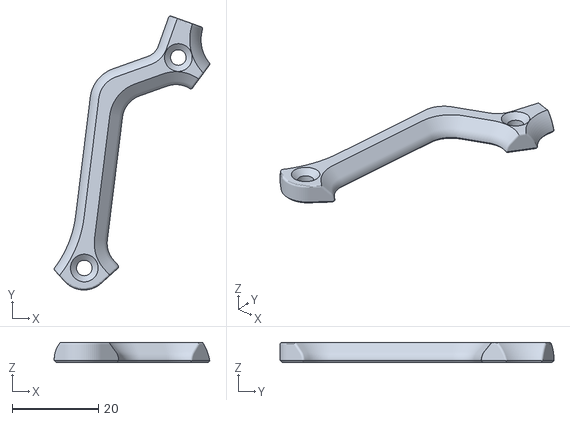
[picture p108: CAD file, 2023-03-18]
SLAB v4 Release/STLs/Orange/LeverBrace.stl
36.1 x 63.5 x 4.65
