Sillybutts/SLAB/SLAB v4 Release/STLs/Orange/Lever_Long.stl

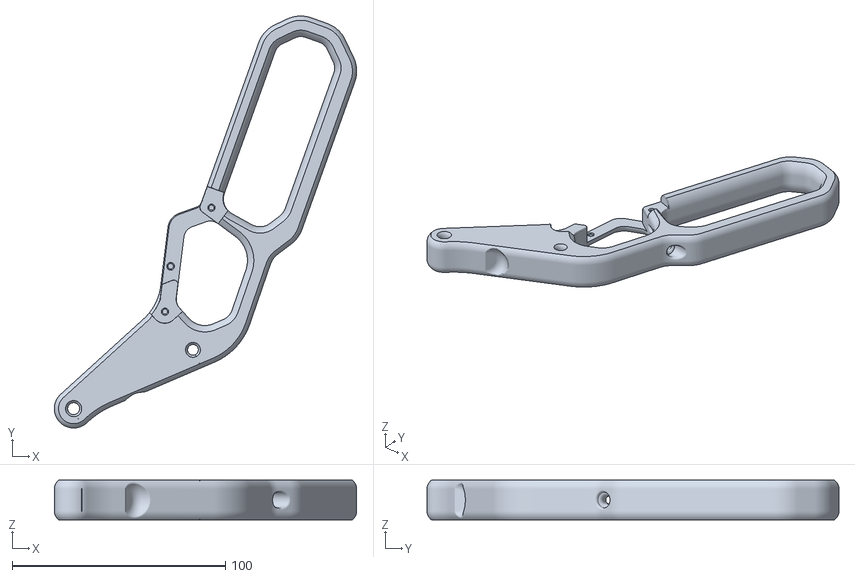
[picture p109: CAD file, 2023-03-18]
SLAB v4 Release/STLs/Orange/Lever_Long.stl
141.9 x 193.4 x 18.5
