Sillybutts/SLAB/v3 BAR BETA VERSION/v3 BAR BETA VERSION STLs/Orange/Bottlenose.stl

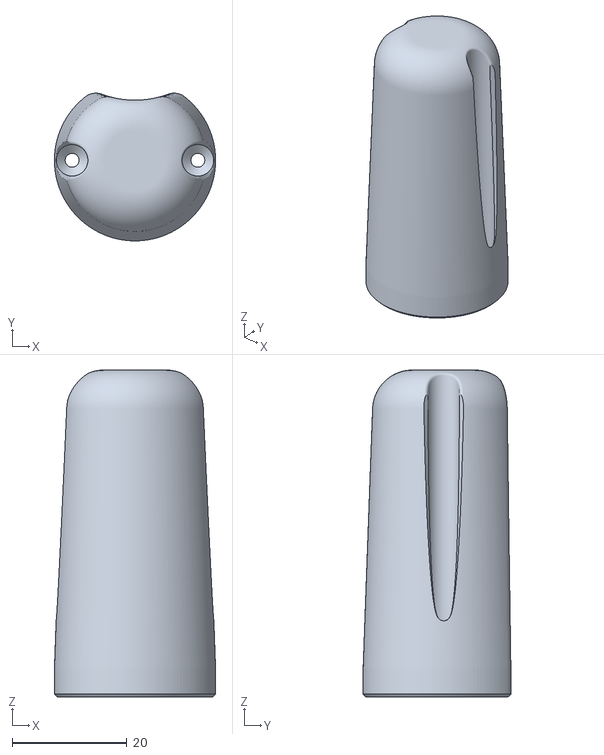
[picture p110: CAD file, 2022-07-20]
v3 BAR BETA VERSION/v3 BAR BETA VERSION STLs/Orange/Bottlenose.stl
28.1 x 25.8 x 57.0
