Sillybutts/SLAB/SLAB v4 Release/STLs/Orange/RodCap.stl

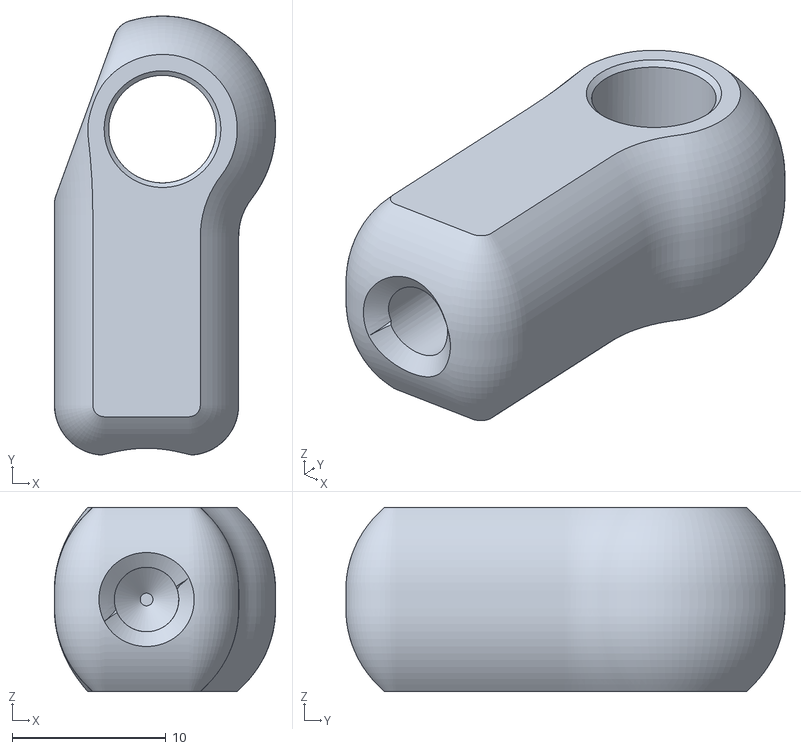
[picture p111: CAD file, 2023-03-18]
SLAB v4 Release/STLs/Orange/RodCap.stl
14.4 x 28.6 x 12.0
