Sillybutts/SLAB/SLAB Metric prints for the V4 3-10-2023/STLs/4.2mm M5 Hole Jig.stl

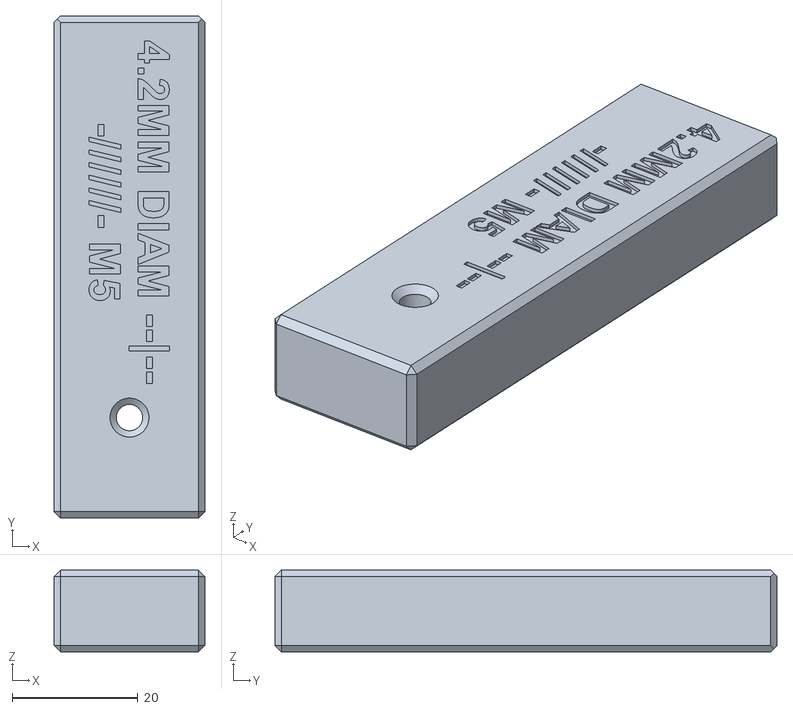
[picture p112: CAD file, 2023-02-27]
SLAB Metric prints for the V4 3-10-2023/STLs/4.2mm M5 Hole Jig.stl
24.0 x 80.0 x 13.0
