Sillybutts/SLAB/SLAB v4 Release/STLs/Green/SidePanel_L.stl

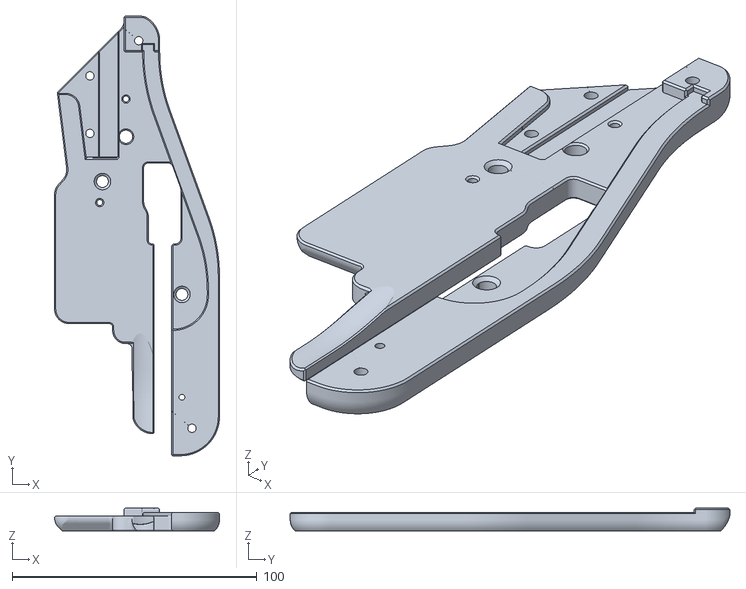
[picture p113: CAD file, 2023-03-18]
SLAB v4 Release/STLs/Green/SidePanel_L.stl
67.4 x 179.6 x 9.25
