Sillybutts/SLAB/v3 BAR BETA VERSION/v3 BAR BETA VERSION STLs/Orange/Lever.stl

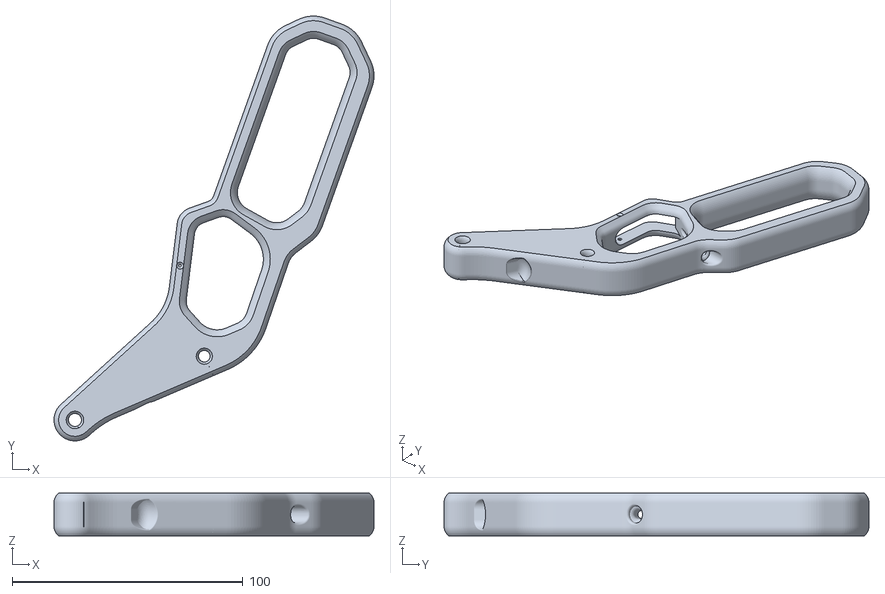
[picture p114: CAD file, 2022-07-20]
v3 BAR BETA VERSION/v3 BAR BETA VERSION STLs/Orange/Lever.stl
138.5 x 183.9 x 18.5
