Sillybutts/SLAB/v3 BAR BETA VERSION/v3 BAR BETA VERSION STLs/Orange/Bottlenose wSling.stl

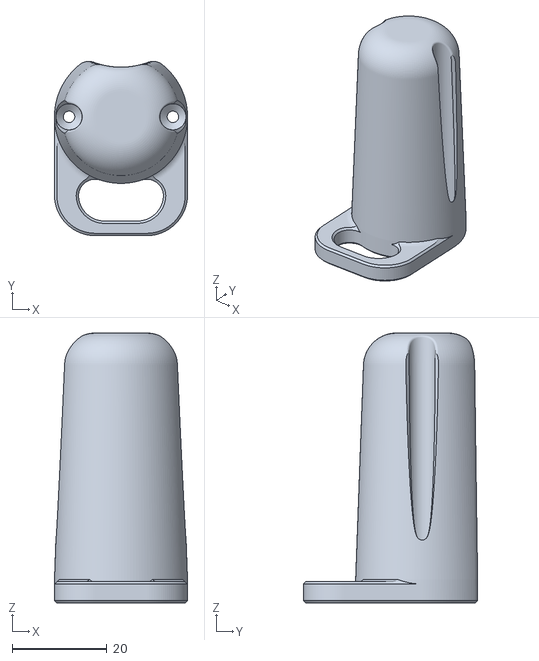
[picture p116: CAD file, 2022-07-20]
v3 BAR BETA VERSION/v3 BAR BETA VERSION STLs/Orange/Bottlenose wSling.stl
28.1 x 36.8 x 57.0
