Sillybutts/SLAB/SLAB v4 Release/STLs/Orange/Lever_Big.stl

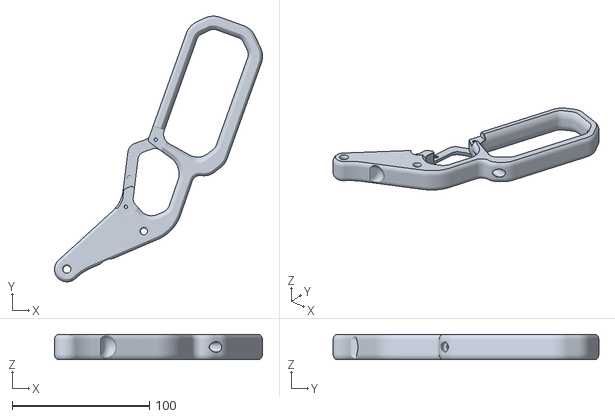
[picture p117: CAD file, 2023-03-18]
SLAB v4 Release/STLs/Orange/Lever_Big.stl
151.3 x 193.4 x 18.5
