Sillybutts/SLAB/SLAB v4 Release/STLs/Green/StockCoreA.stl

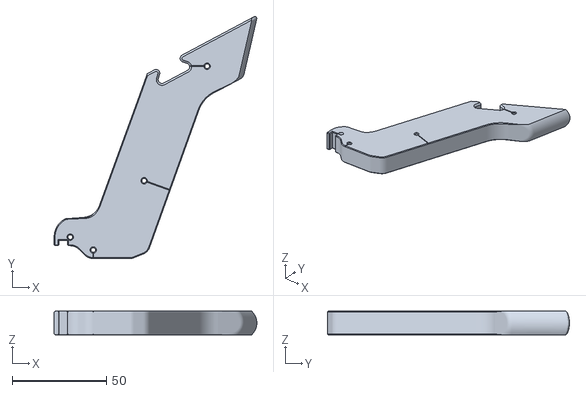
[picture p118: CAD file, 2023-03-18]
SLAB v4 Release/STLs/Green/StockCoreA.stl
107.5 x 128.3 x 12.7
