Sillybutts/SLAB/SLAB v4 Release/STLs/Orange/Trigger.stl

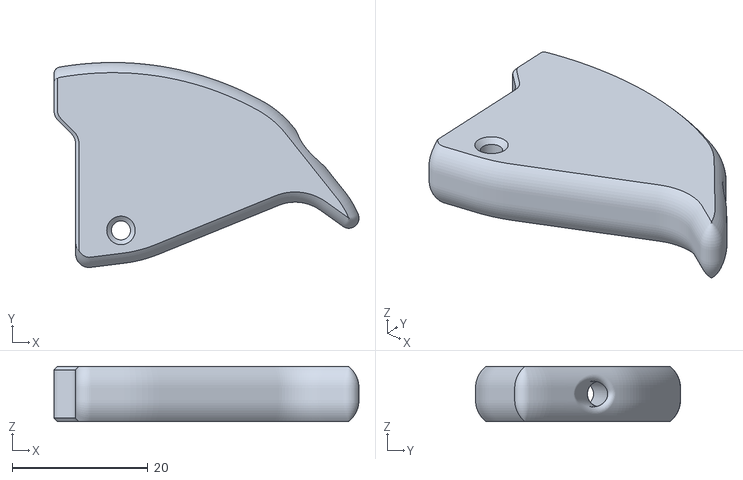
[picture p119: CAD file, 2023-03-18]
SLAB v4 Release/STLs/Orange/Trigger.stl
44.9 x 30.2 x 8.12
