Sillybutts/SLAB/v3 BAR BETA VERSION/v3 BAR BETA VERSION STLs/Green/StockCoreC wSling.stl

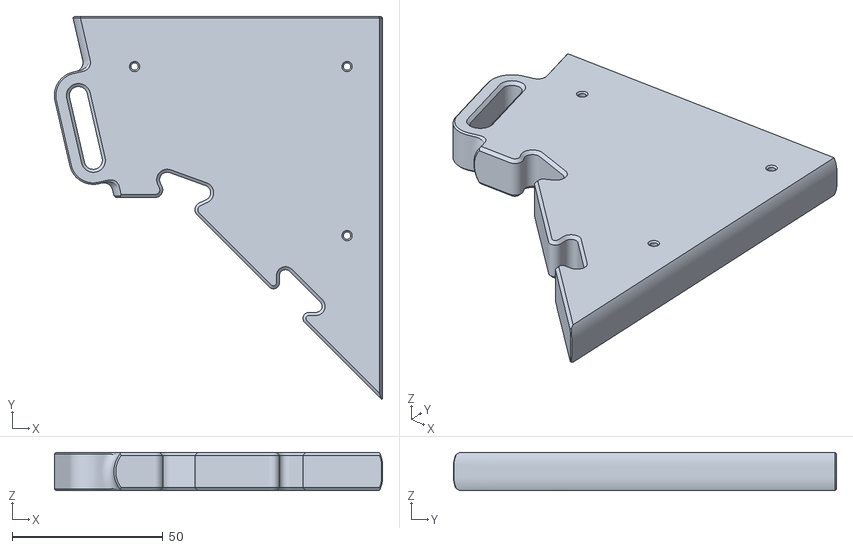
[picture p120: CAD file, 2022-06-17]
v3 BAR BETA VERSION/v3 BAR BETA VERSION STLs/Green/StockCoreC wSling.stl
108.9 x 127.0 x 12.7
