Sillybutts/SLAB/SLAB v4 Release/STLs/Green/Handguard.stl

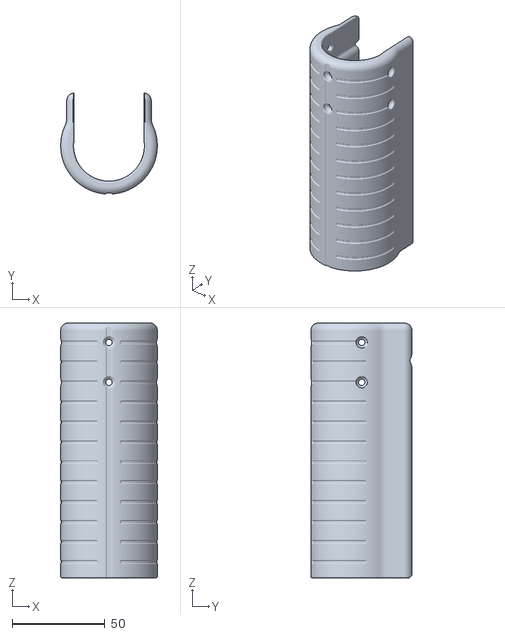
[picture p121: CAD file, 2023-03-18]
SLAB v4 Release/STLs/Green/Handguard.stl
52.1 x 54.4 x 137.4
