Sillybutts/SLAB/SLAB v4 Release/STLs/Orange/PlungerHead.stl

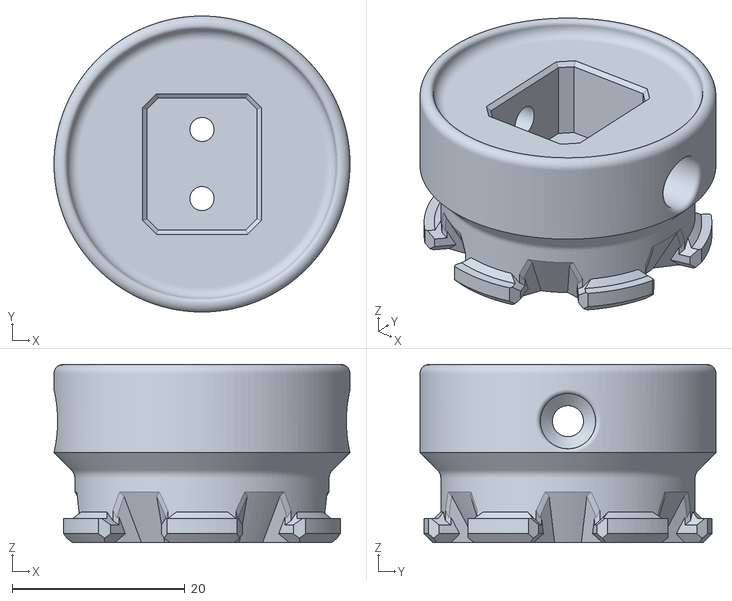
[picture p122: CAD file, 2023-03-18]
SLAB v4 Release/STLs/Orange/PlungerHead.stl
34.3 x 34.3 x 20.6
