Sillybutts/SLAB/SLAB v4 Release/STLs/Green/Handguard wPicatinny.stl

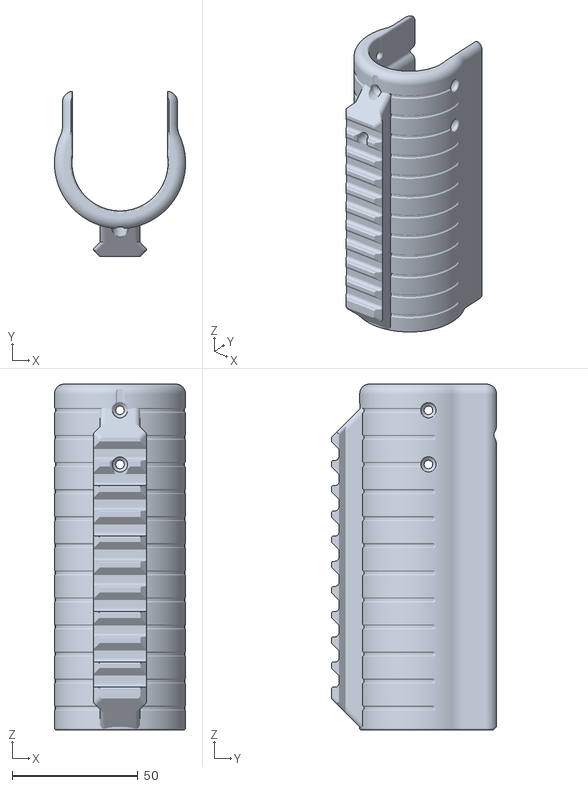
[picture p123: CAD file, 2023-03-18]
SLAB v4 Release/STLs/Green/Handguard wPicatinny.stl
52.1 x 65.6 x 137.4
