Sillybutts/SLAB/SLAB v4 Release/STLs/Orange/CatchPusher.stl

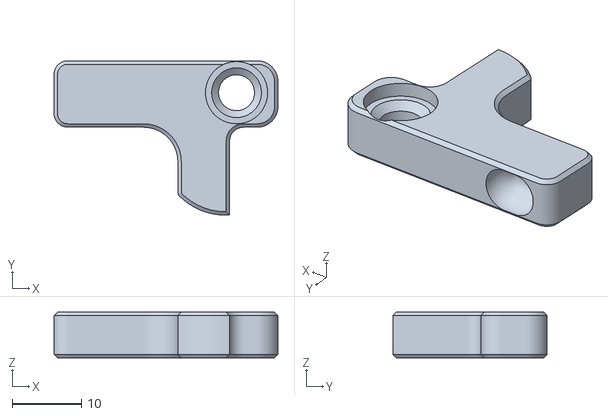
[picture p124: CAD file, 2023-03-18]
SLAB v4 Release/STLs/Orange/CatchPusher.stl
32.4 x 22.4 x 6.60
