Sillybutts/SLAB/SLAB v4 Release/STLs/Green/StockCoreC Slingless.stl

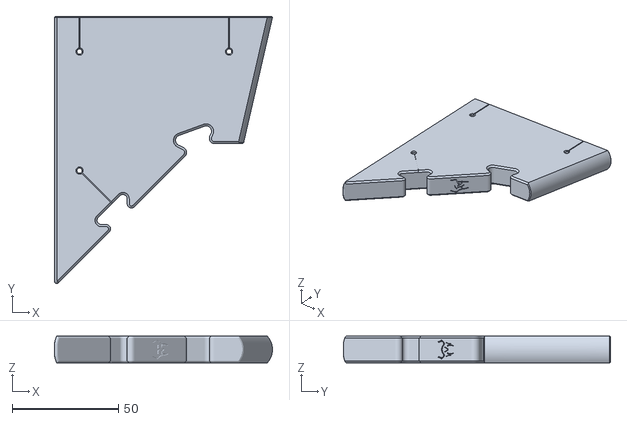
[picture p125: CAD file, 2023-03-18]
SLAB v4 Release/STLs/Green/StockCoreC Slingless.stl
102.7 x 125.9 x 12.7
