Sillybutts/SLAB/SLAB v4 Release/STLs/Orange/Lever_Standard.stl

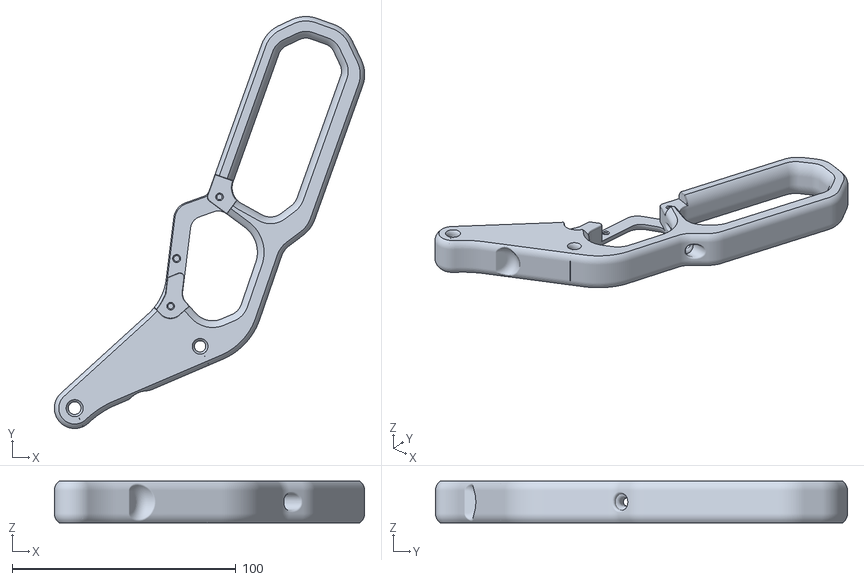
[picture p126: CAD file, 2023-03-18]
SLAB v4 Release/STLs/Orange/Lever_Standard.stl
138.6 x 183.9 x 18.5
