Sillybutts/SLAB/SLAB v4 Release/STLs/Orange/MagRelease.stl

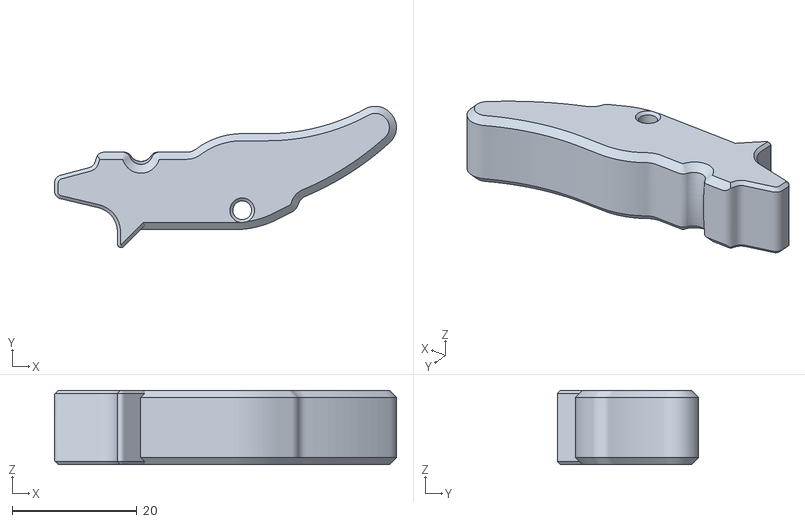
[picture p127: CAD file, 2023-03-18]
SLAB v4 Release/STLs/Orange/MagRelease.stl
54.9 x 22.7 x 11.9
