Sillybutts/SLAB/SLAB v4 Release/STLs/Orange/Catch_Tighter.stl

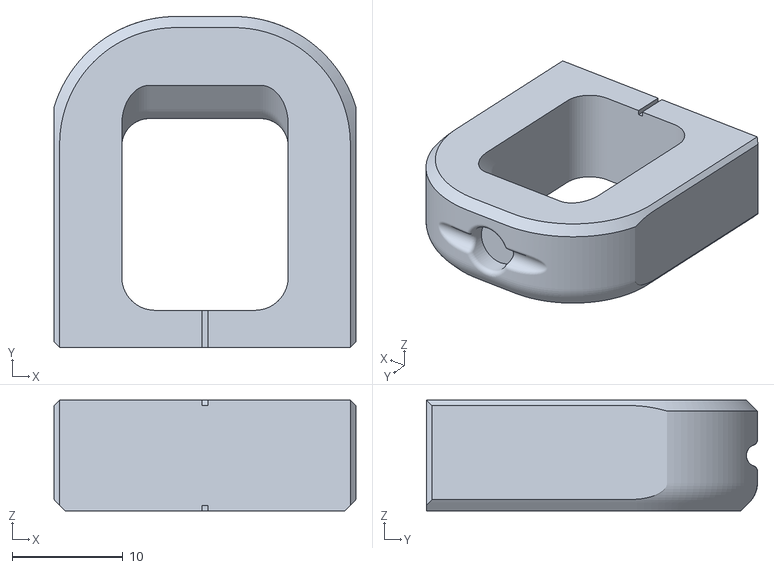
[picture p128: CAD file, 2023-03-18]
SLAB v4 Release/STLs/Orange/Catch_Tighter.stl
27.2 x 29.8 x 10.0
