Sillybutts/SLAB/SLAB v4 Release/STLs/Orange/Muzzle_FrontSling.stl

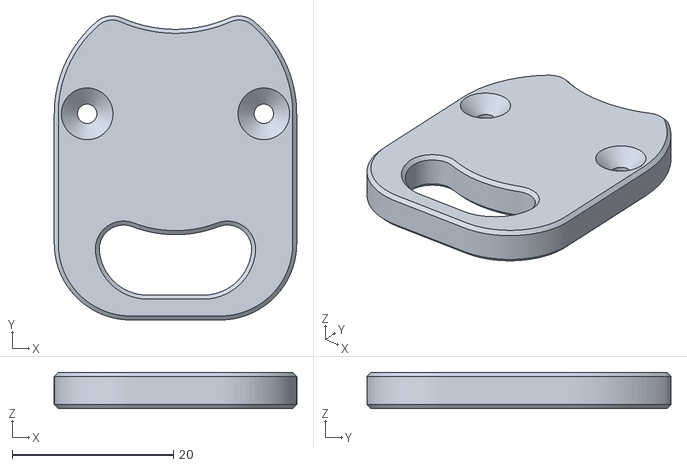
[picture p129: CAD file, 2023-03-18]
SLAB v4 Release/STLs/Orange/Muzzle_FrontSling.stl
30.1 x 37.7 x 4.50
